Vprince099/ZANDVE/Type-Z/STLs/Panels/Front/README.md

# Credits 
* Parts retrofitted from Voron Trident [VoronDesign](https://github.com/VoronDesign/)
* Adapted to include accent pieces since front frame is 2040
