Vprince099/ZANDVE/User_Mods/LTSPENNY/ZANDVE/L_Stepper_Pillow_Bearing/Images/IMG3.JPG

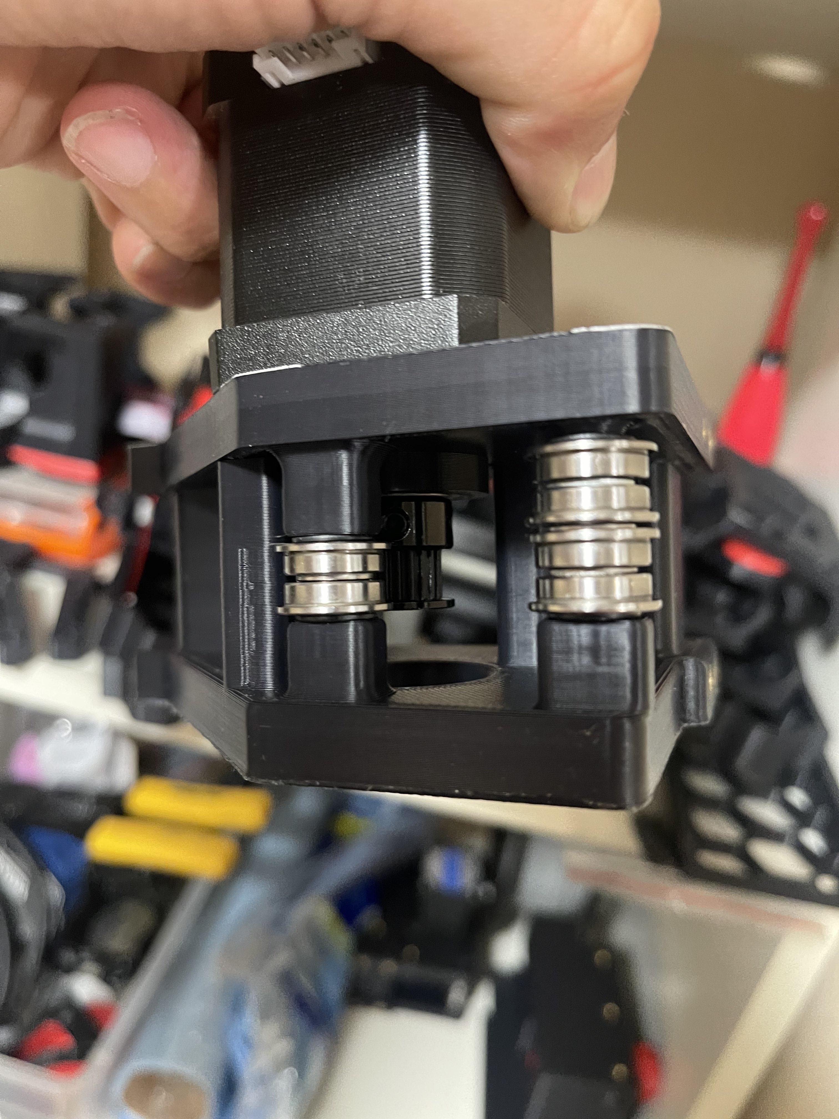
User_Mods/LTSPENNY/ZANDVE/L_Stepper_Pillow_Bearing/Images/IMG3.JPG
