Vprince099/ZANDVE/Type-V/STLs/Panels/Rear/Corner Panel Retainer 3mm x2.stl

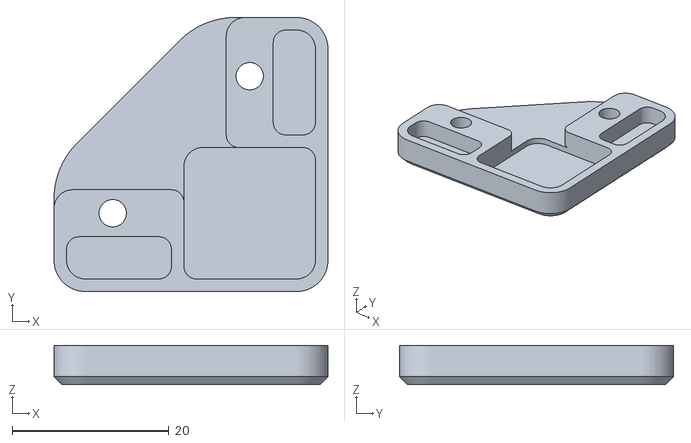
[picture p20: CAD file, 2023-03-26]
Type-V/STLs/Panels/Rear/Corner Panel Retainer 3mm x2.stl
35.0 x 35.0 x 5.00
