Vprince099/ZANDVE/Type-V/STLs/Skirt/PostBuild_Parts/Bottom Panel/bottom_panel_hinge_x2.stl

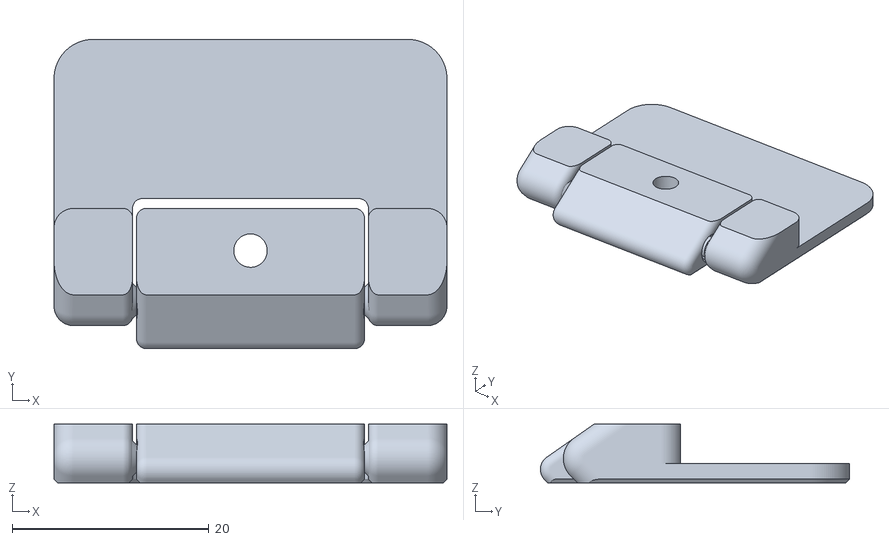
[picture p21: CAD file, 2023-04-10]
Type-V/STLs/Skirt/PostBuild_Parts/Bottom Panel/bottom_panel_hinge_x2.stl
40.0 x 31.5 x 6.00
