Vprince099/ZANDVE/Type-V/STLs/Skirt/PostBuild_Parts/Front/[a]_skirt_logo_x2.stl

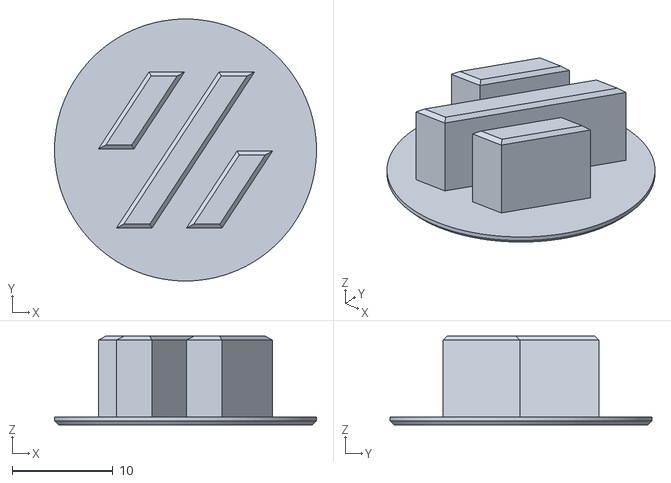
[picture p22: CAD file, 2023-04-05]
Type-V/STLs/Skirt/PostBuild_Parts/Front/[a]_skirt_logo_x2.stl
26.0 x 26.0 x 8.80
