Vprince099/ZANDVE/Type-V/STLs/Skirt/PostBuild_Parts/Rear/Rear_Center_Skirt_E5Plus_Type_V.stl

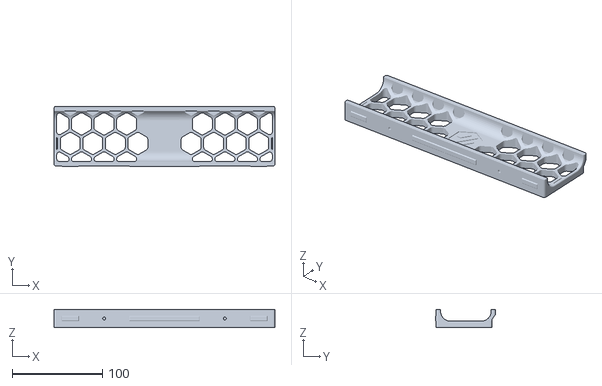
[picture p23: CAD file, 2023-04-05]
Type-V/STLs/Skirt/PostBuild_Parts/Rear/Rear_Center_Skirt_E5Plus_Type_V.stl
245.0 x 66.8 x 20.0
