Vprince099/ZANDVE/Type-V/STLs/Skirt/PostBuild_Parts/Sides/[a]_fan_grill_b_x2.stl

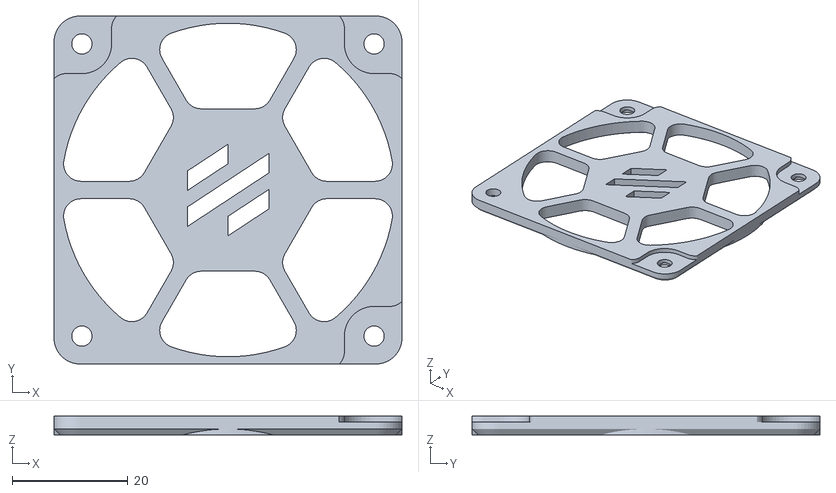
[picture p24: CAD file, 2023-04-05]
Type-V/STLs/Skirt/PostBuild_Parts/Sides/[a]_fan_grill_b_x2.stl
60.0 x 60.0 x 3.20
