Vprince099/ZANDVE/Type-V/STLs/Skirt/PreBuild_Parts/Corners/[a]_corner_baseplate_b_x2.stl

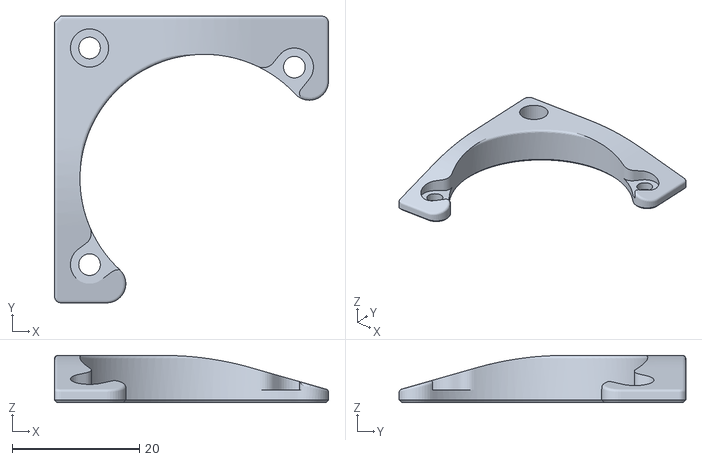
[picture p25: CAD file, 2023-03-27]
Type-V/STLs/Skirt/PreBuild_Parts/Corners/[a]_corner_baseplate_b_x2.stl
43.0 x 45.0 x 7.40
