Vprince099/ZANDVE/Type-V/STLs/Skirt/PreBuild_Parts/Screen/[a]_mini12864_case_front_insert.stl

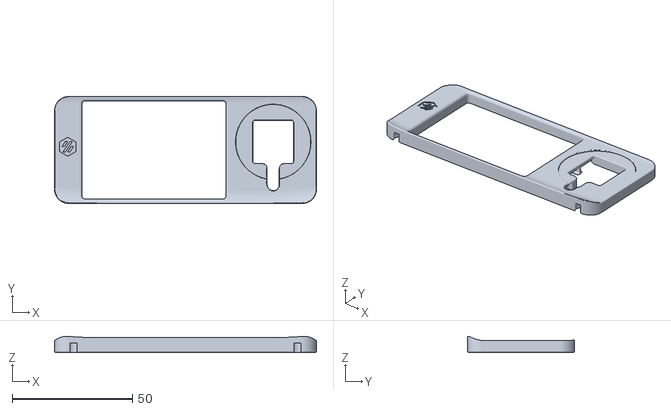
[picture p27: CAD file, 2023-04-05]
Type-V/STLs/Skirt/PreBuild_Parts/Screen/[a]_mini12864_case_front_insert.stl
109.0 x 44.6 x 6.81
