Vprince099/ZANDVE/Type-V/STLs/Tension_Towers/Left/L_Frame_Enclosure_WSupp.stl

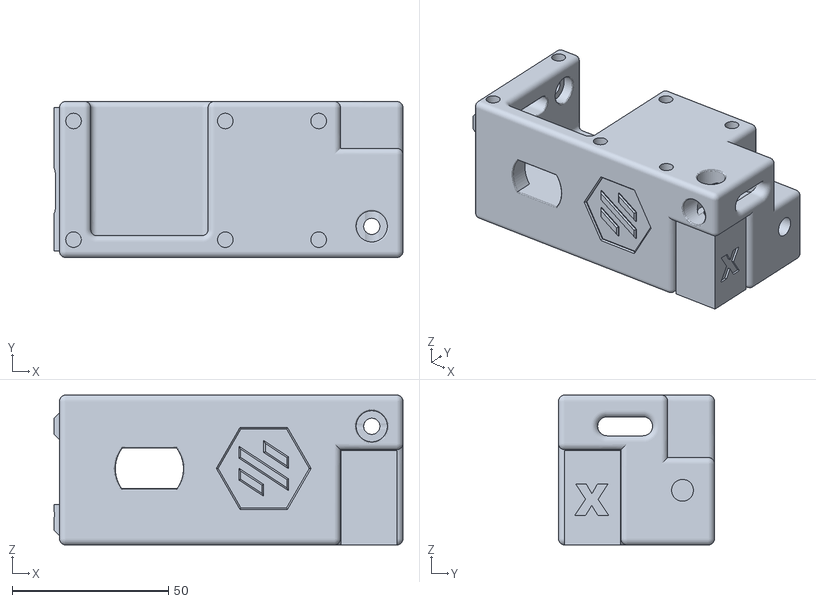
[picture p28: CAD file, 2023-04-05]
Type-V/STLs/Tension_Towers/Left/L_Frame_Enclosure_WSupp.stl
111.8 x 50.0 x 48.0
