Vprince099/ZANDVE/Type-V/STLs/Tools/ZeroGCube30x30.stl

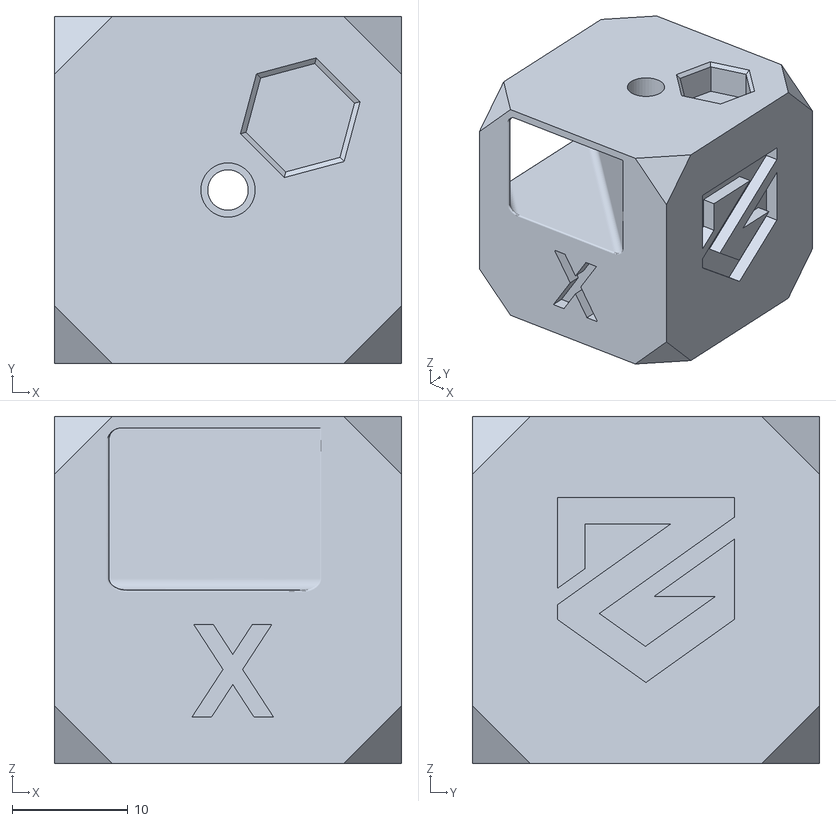
[picture p29: CAD file, 2023-03-27]
Type-V/STLs/Tools/ZeroGCube30x30.stl
30.0 x 30.0 x 30.0
