Vprince099/ZANDVE/Type-V/STLs/Top_Hat_STD/TH_Front_Left/FL Front Panel Lid[acc].stl

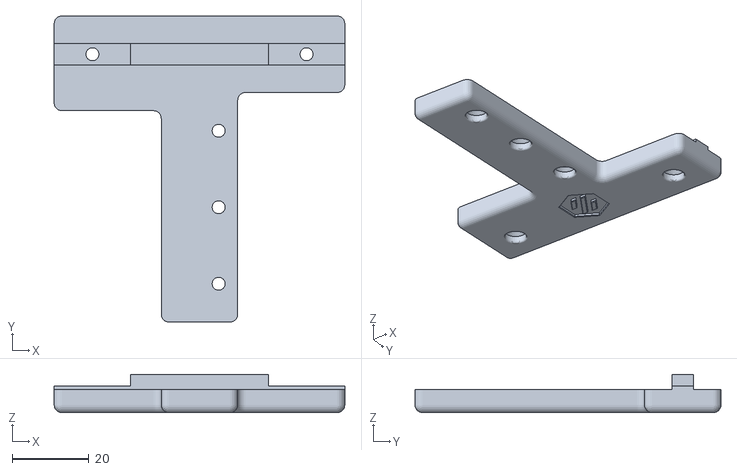
[picture p30: CAD file, 2023-04-05]
Type-V/STLs/Top_Hat_STD/TH_Front_Left/FL Front Panel Lid[acc].stl
76.0 x 80.0 x 10.0
