Vprince099/ZANDVE/Type-V/STLs/Top_Hat_STD/TH_Rear/Rear Panel - Right.stl

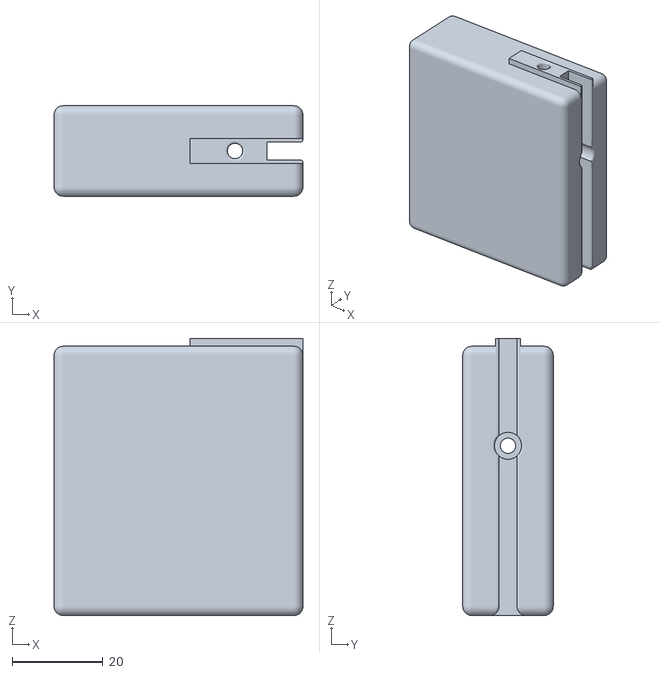
[picture p31: CAD file, 2023-03-26]
Type-V/STLs/Top_Hat_STD/TH_Rear/Rear Panel - Right.stl
55.0 x 20.0 x 61.2
