Vprince099/ZANDVE/Type-V/STLs/Top_Hat_STD/TH_Rear_Left/RL Corner With Support.stl

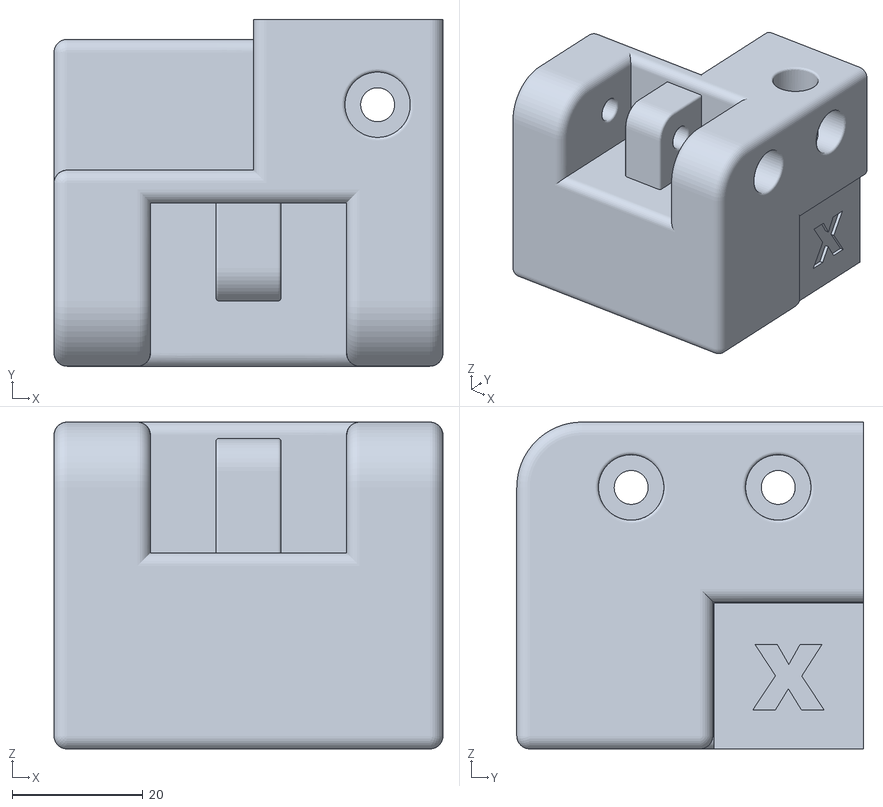
[picture p32: CAD file, 2023-04-02]
Type-V/STLs/Top_Hat_STD/TH_Rear_Left/RL Corner With Support.stl
59.5 x 53.0 x 50.0
