Vprince099/ZANDVE/Type-V/STLs/Top_Hat_XL/TH_Rear/Rear Panel - Center.stl

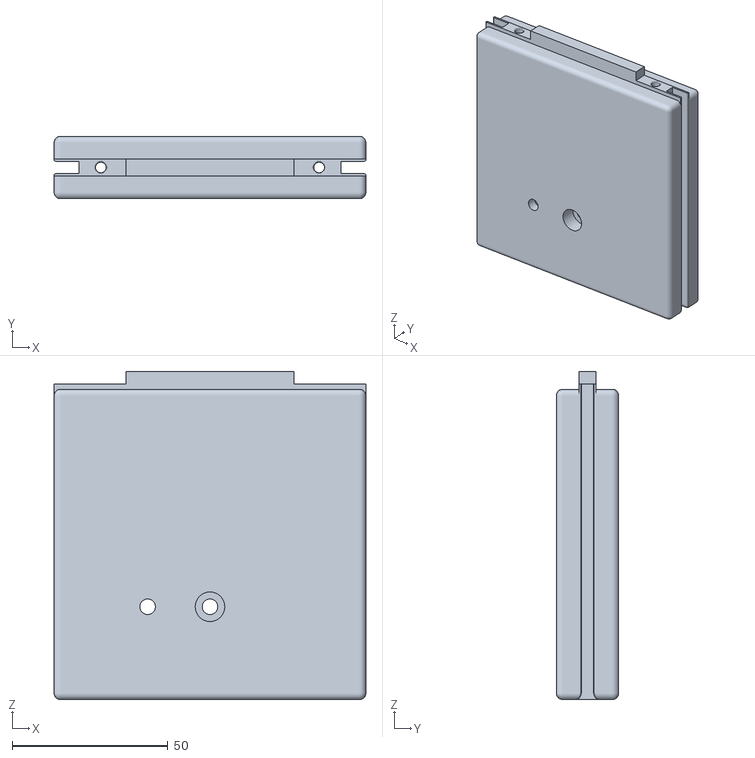
[picture p34: CAD file, 2023-04-01]
Type-V/STLs/Top_Hat_XL/TH_Rear/Rear Panel - Center.stl
100.0 x 20.0 x 105.2
