Vprince099/ZANDVE/Type-V/STLs/X-Gantry/Left/L_Top_Left.stl

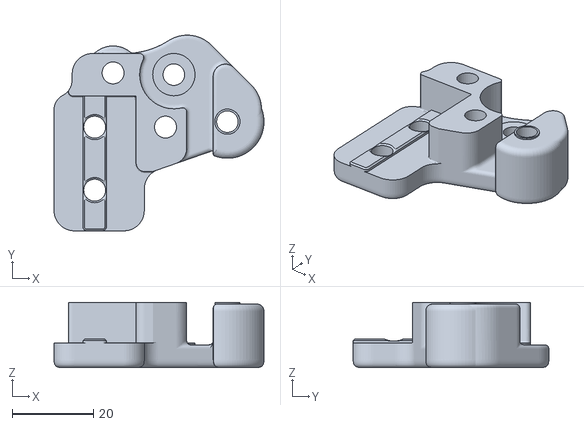
[picture p35: CAD file, 2023-03-27]
Type-V/STLs/X-Gantry/Left/L_Top_Left.stl
51.6 x 48.1 x 16.0
