Vprince099/ZANDVE/Type-V/STLs/X-Gantry/Right/R_Bottom_right.stl

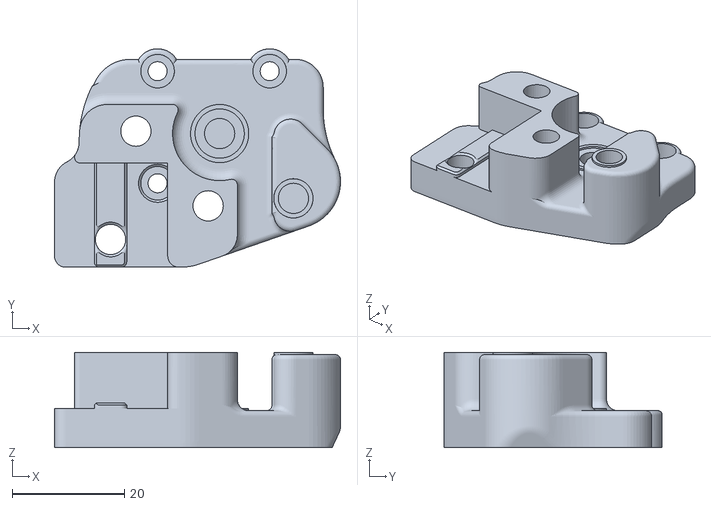
[picture p36: CAD file, 2023-03-27]
Type-V/STLs/X-Gantry/Right/R_Bottom_right.stl
51.0 x 39.0 x 17.0
