Vprince099/ZANDVE/Type-V/STLs/Z_Motion/wago_221-412_mount.stl

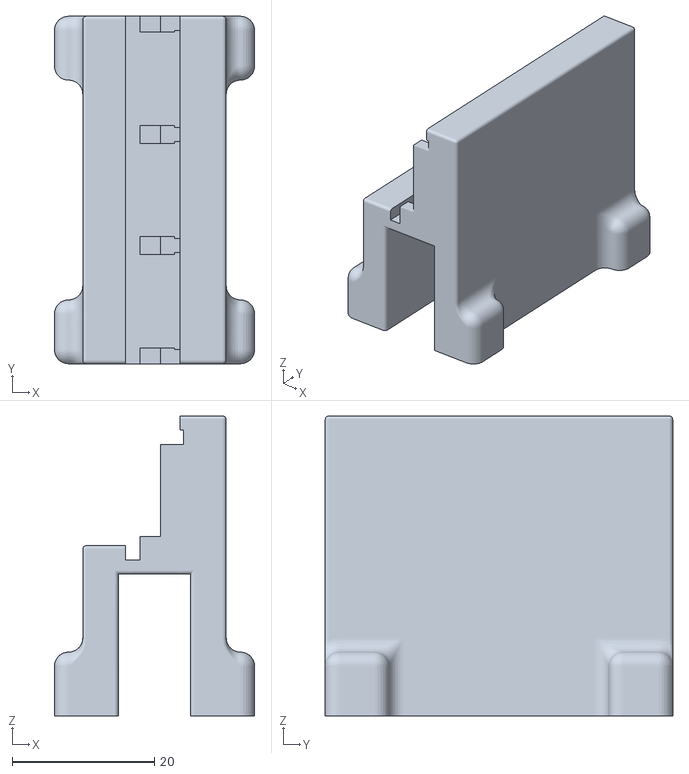
[picture p37: CAD file, 2023-03-27]
Type-V/STLs/Z_Motion/wago_221-412_mount.stl
28.2 x 49.0 x 42.2
