Vprince099/ZANDVE/Type-Z/STLs/Limit_Switch_Mounts/Klicky Dock Mount.stl

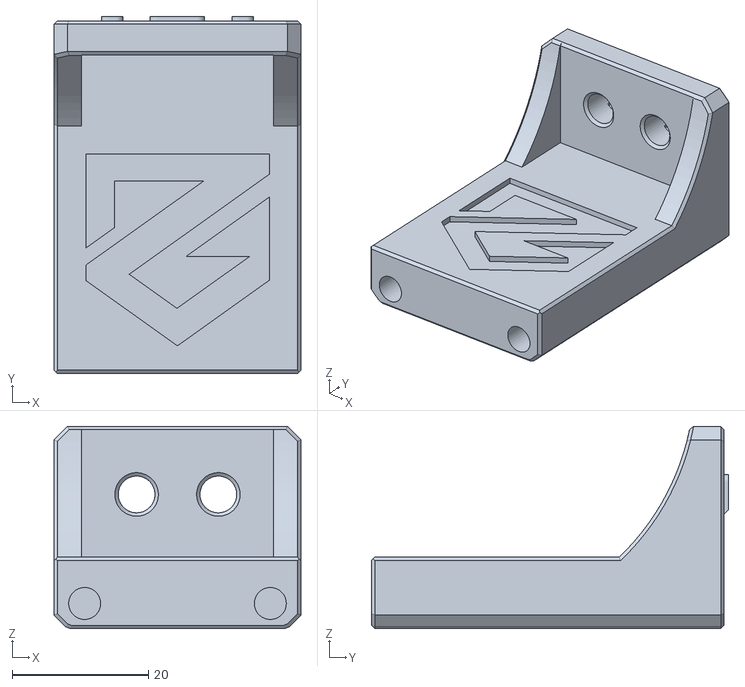
[picture p38: CAD file, 2023-03-27]
Type-Z/STLs/Limit_Switch_Mounts/Klicky Dock Mount.stl
36.3 x 52.4 x 29.7
