Vprince099/ZANDVE/Type-Z/STLs/Panels/Gantry/Rear/Rear Panel Base - Left.stl

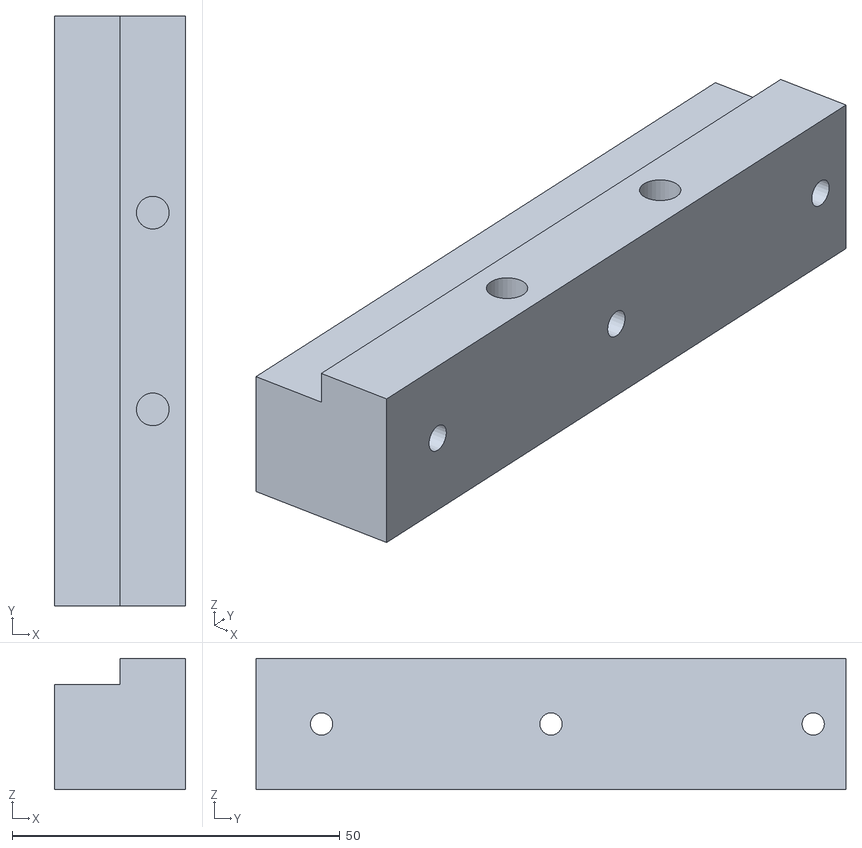
[picture p39: CAD file, 2023-05-07]
Type-Z/STLs/Panels/Gantry/Rear/Rear Panel Base - Left.stl
20.0 x 90.0 x 20.0
