Vprince099/ZANDVE/Type-Z/STLs/Panels/Rear/Type-Z_2020_Endcap_Cover.stl

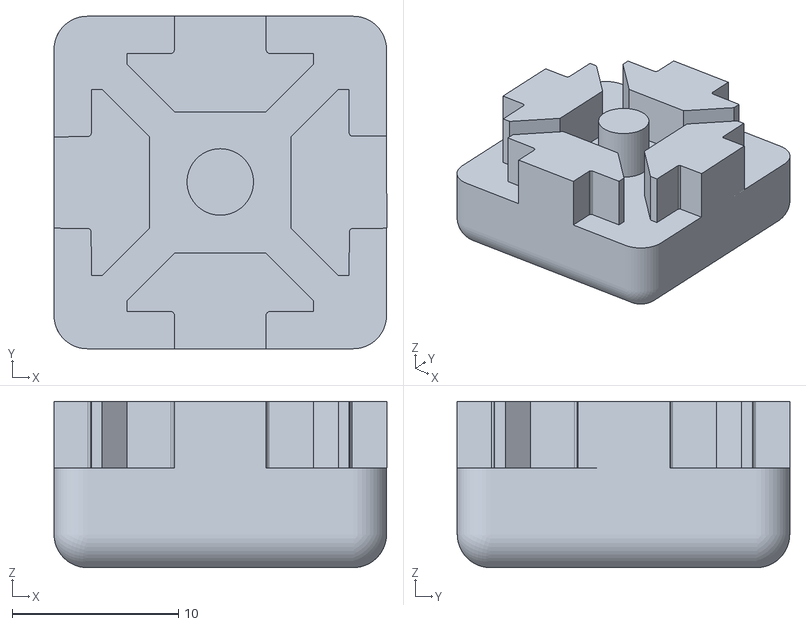
[picture p40: CAD file, 2023-03-27]
Type-Z/STLs/Panels/Rear/Type-Z_2020_Endcap_Cover.stl
20.0 x 20.0 x 10.0
