Vprince099/ZANDVE/Type-Z/STLs/Rear_Steppers/Max Power/Left/L Bottom Plate MP.stl

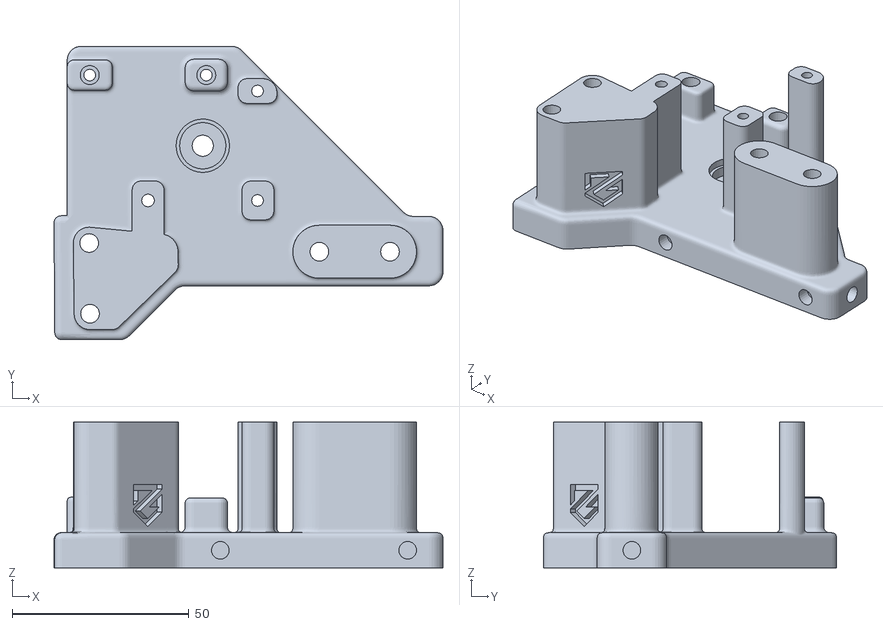
[picture p41: CAD file, 2023-05-07]
Type-Z/STLs/Rear_Steppers/Max Power/Left/L Bottom Plate MP.stl
110.1 x 83.1 x 41.3
