Vprince099/ZANDVE/Type-Z/STLs/Skirt/PostBuild_Parts/Front/ZeroG Insert Right[acc].stl

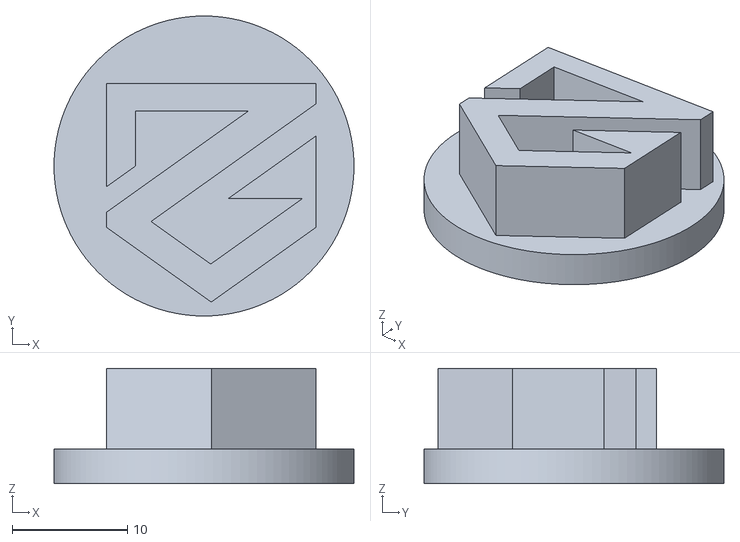
[picture p43: CAD file, 2023-03-27]
Type-Z/STLs/Skirt/PostBuild_Parts/Front/ZeroG Insert Right[acc].stl
26.0 x 26.0 x 10.0
