Vprince099/ZANDVE/Type-Z/STLs/Skirt/PostBuild_Parts/Sides/[a]type_z_fan_grill_a_x2.stl

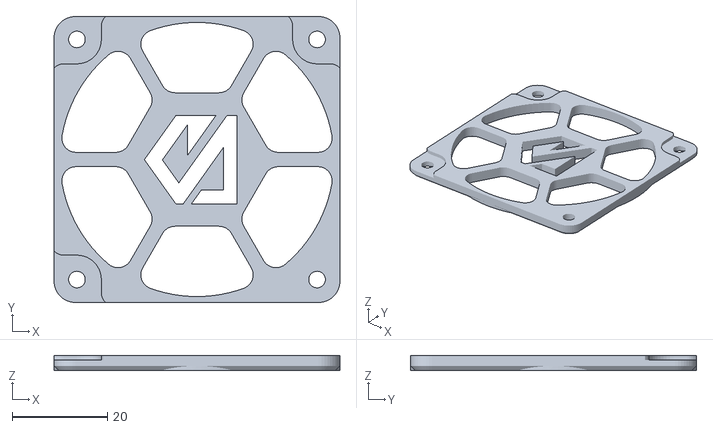
[picture p44: CAD file, 2023-03-27]
Type-Z/STLs/Skirt/PostBuild_Parts/Sides/[a]type_z_fan_grill_a_x2.stl
60.0 x 60.0 x 3.20
