Vprince099/ZANDVE/Type-Z/STLs/Top_Hat/TH_Rear_Left/RR Panel Base.stl

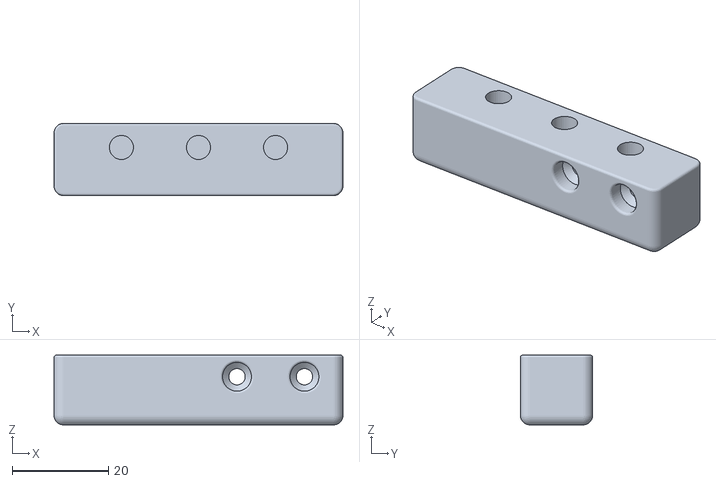
[picture p45: CAD file, 2023-03-26]
Type-Z/STLs/Top_Hat/TH_Rear_Left/RR Panel Base.stl
60.0 x 15.0 x 14.5
