Vprince099/ZANDVE/User_Mods/JellyBob/ZANDVE_Less-Frame/STL's/L_Less_Frame_Enclosure_WSupp.stl

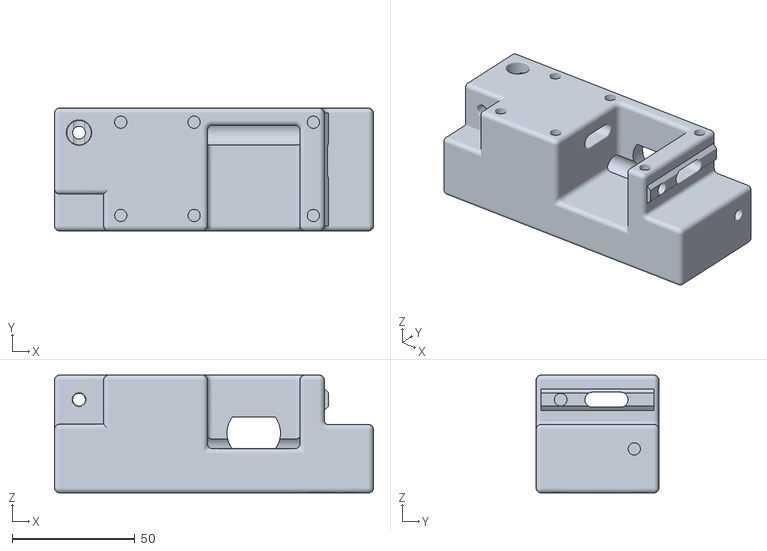
[picture p46: CAD file, 2023-04-02]
User_Mods/JellyBob/ZANDVE_Less-Frame/STL's/L_Less_Frame_Enclosure_WSupp.stl
130.0 x 50.0 x 48.0
