Vprince099/ZANDVE/User_Mods/LTSPENNY/ZANDVE/L_Stepper_Pillow_Bearing/STLs/Left_Stepper_Pillow_Block_Mod.stl

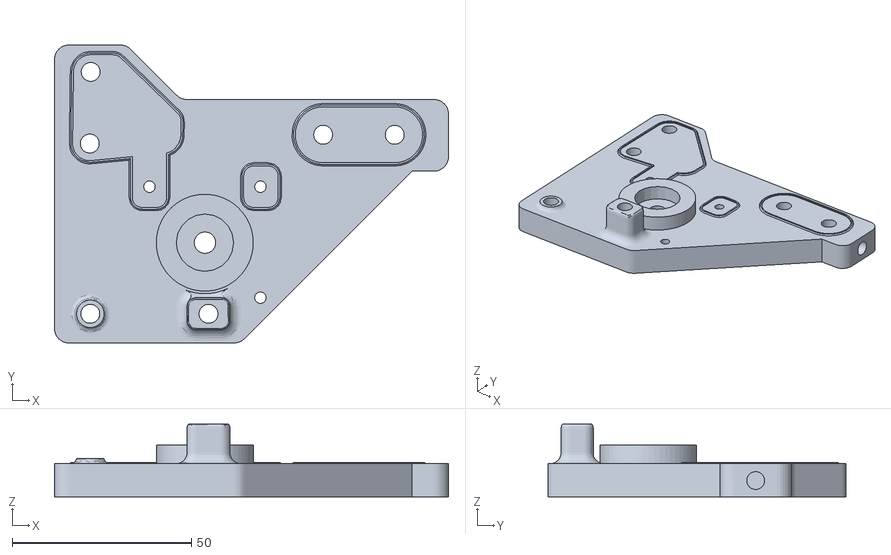
[picture p47: CAD file, 2023-04-13]
User_Mods/LTSPENNY/ZANDVE/L_Stepper_Pillow_Bearing/STLs/Left_Stepper_Pillow_Block_Mod.stl
110.0 x 83.2 x 20.3
