Vprince099/ZANDVE/Type-V/STLs/Electronics/DIN_frame_mount_x4_corrected.stl

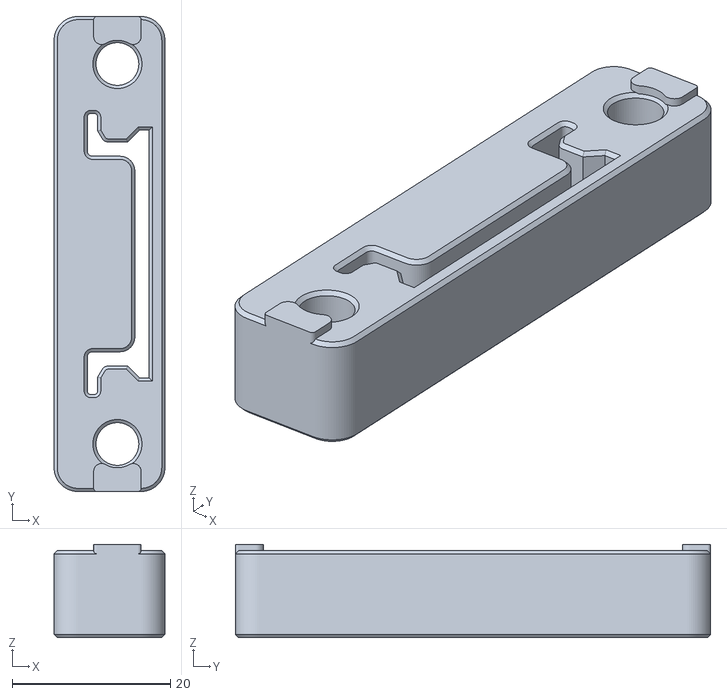
[picture p48: CAD file, 2023-03-27]
Type-V/STLs/Electronics/DIN_frame_mount_x4_corrected.stl
14.0 x 60.0 x 11.8
