Vprince099/ZANDVE/Type-V/STLs/Limit_Switch_Mounts/X Endstop.stl

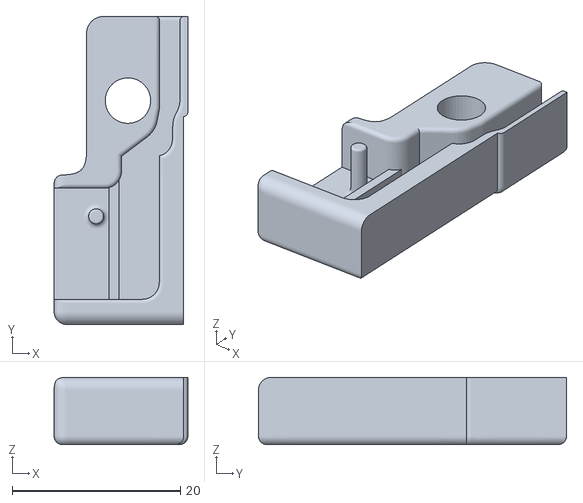
[picture p49: CAD file, 2023-03-27]
Type-V/STLs/Limit_Switch_Mounts/X Endstop.stl
15.9 x 36.6 x 8.00
