Vprince099/ZANDVE/Type-V/STLs/Panels/Front/Hinge_Cover_Top_Left[acc].stl

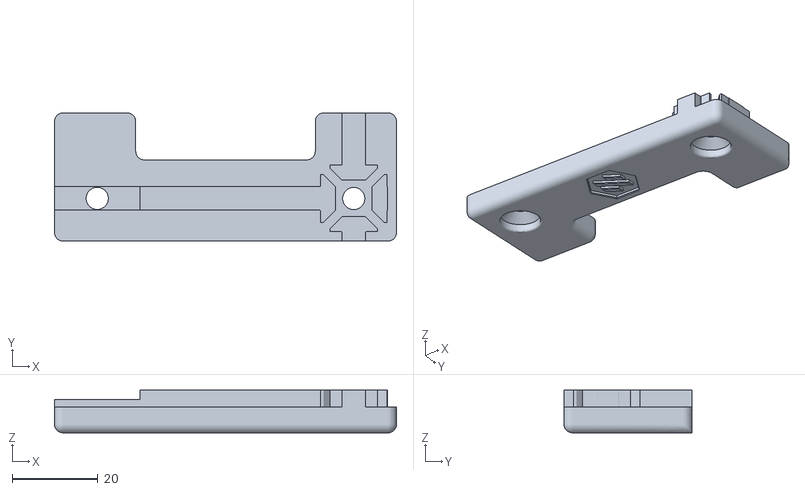
[picture p50: CAD file, 2023-04-05]
Type-V/STLs/Panels/Front/Hinge_Cover_Top_Left[acc].stl
80.0 x 30.0 x 10.0
