Vprince099/ZANDVE/Type-V/STLs/Panels/Gantry/Left/Rear Panel Lid.stl

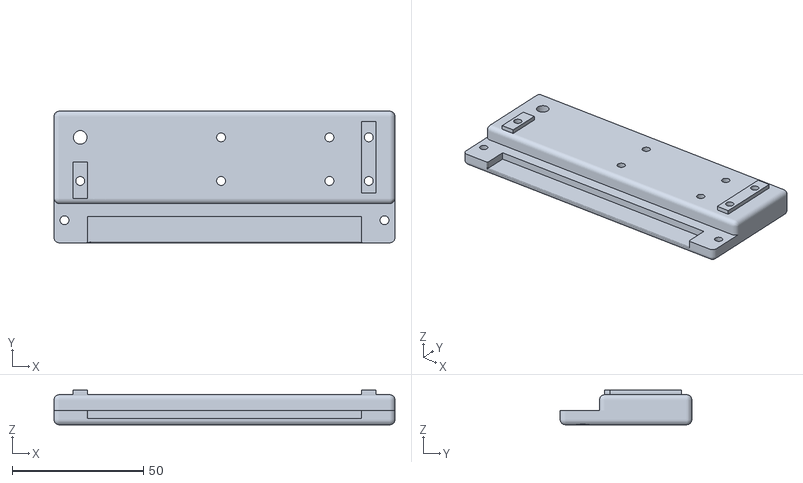
[picture p51: CAD file, 2023-03-26]
Type-V/STLs/Panels/Gantry/Left/Rear Panel Lid.stl
130.0 x 50.2 x 13.2
