Vprince099/ZANDVE/Type-V/STLs/Panels/Gantry/Right/X Panel Lid x8.stl

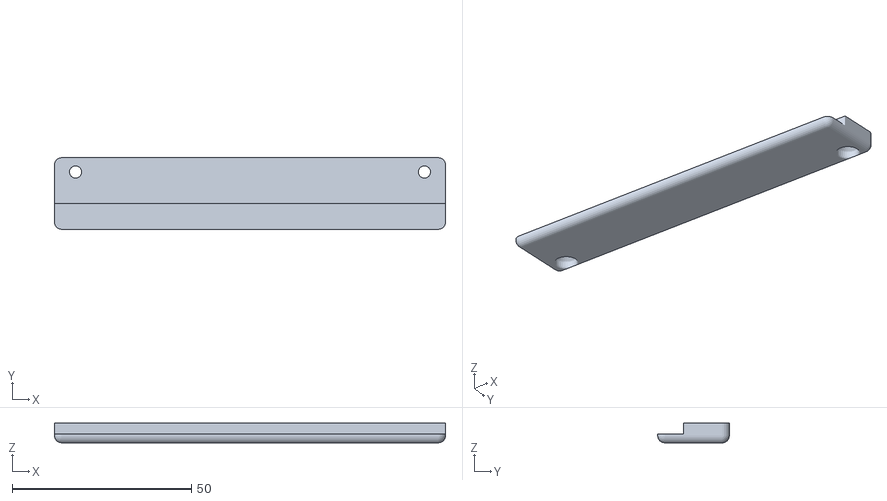
[picture p52: CAD file, 2023-03-26]
Type-V/STLs/Panels/Gantry/Right/X Panel Lid x8.stl
109.0 x 20.0 x 5.50
