Vprince099/ZANDVE/Type-V/STLs/Skirt/PostBuild_Parts/Bottom Panel/bottom_panel_clip_x4.stl

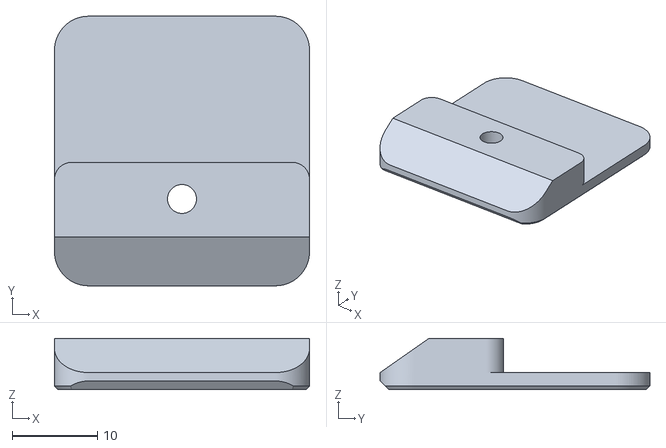
[picture p53: CAD file, 2023-04-10]
Type-V/STLs/Skirt/PostBuild_Parts/Bottom Panel/bottom_panel_clip_x4.stl
30.0 x 31.7 x 6.00
