Vprince099/ZANDVE/Type-V/STLs/Skirt/PostBuild_Parts/Front/Skirt_E5+_Front_Left.stl

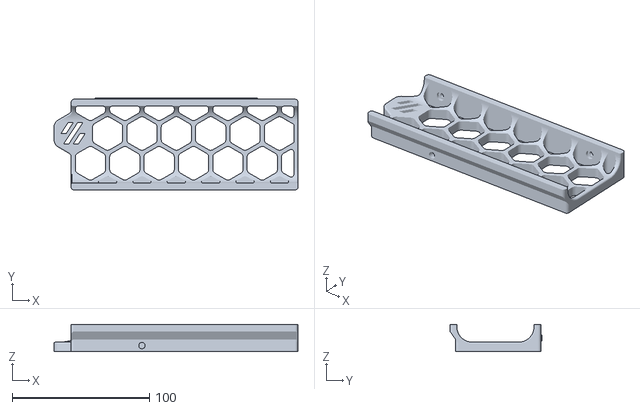
[picture p54: CAD file, 2023-04-05]
Type-V/STLs/Skirt/PostBuild_Parts/Front/Skirt_E5+_Front_Left.stl
177.5 x 66.8 x 20.0
