Vprince099/ZANDVE/Type-V/STLs/Skirt/PreBuild_Parts/Rear_IO/keystone_panel.stl

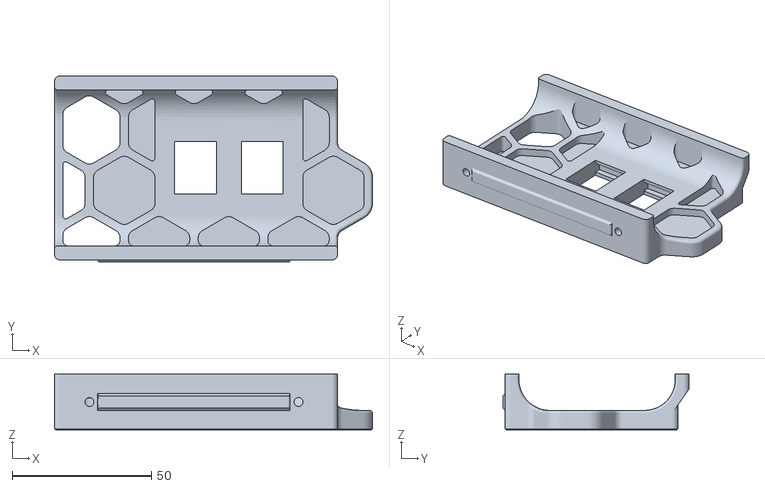
[picture p55: CAD file, 2023-03-27]
Type-V/STLs/Skirt/PreBuild_Parts/Rear_IO/keystone_panel.stl
114.0 x 66.8 x 20.0
