Vprince099/ZANDVE/Type-V/STLs/Skirt/PreBuild_Parts/Screen/mini12864_case_rear.stl

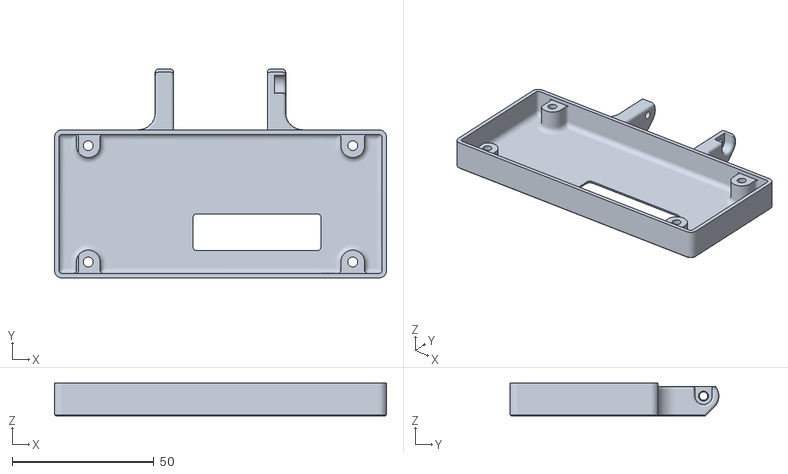
[picture p56: CAD file, 2023-03-27]
Type-V/STLs/Skirt/PreBuild_Parts/Screen/mini12864_case_rear.stl
117.0 x 73.6 x 11.6
