Vprince099/ZANDVE/Type-V/STLs/Tension_Towers/Left/L_Tensioner[acc].stl

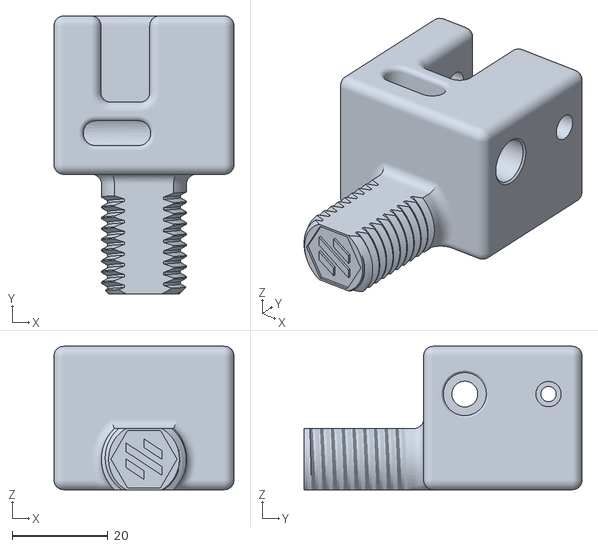
[picture p57: CAD file, 2023-04-05]
Type-V/STLs/Tension_Towers/Left/L_Tensioner[acc].stl
37.6 x 58.1 x 30.0
