Vprince099/ZANDVE/Type-V/STLs/Tools/Rail alignment tool x 2.stl

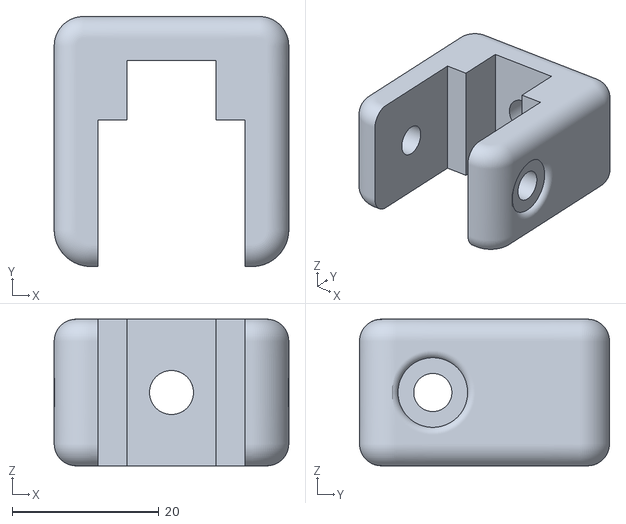
[picture p58: CAD file, 2023-03-27]
Type-V/STLs/Tools/Rail alignment tool x 2.stl
32.0 x 34.1 x 20.0
