Vprince099/ZANDVE/Type-V/STLs/Top_Hat_STD/TH_Front_Left/FL Inner Panel Lid.stl

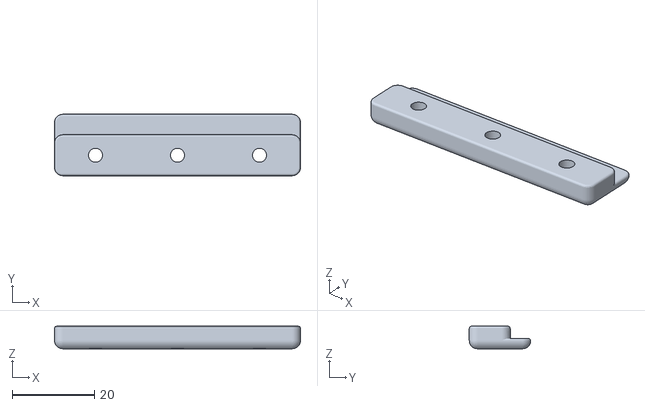
[picture p59: CAD file, 2023-03-26]
Type-V/STLs/Top_Hat_STD/TH_Front_Left/FL Inner Panel Lid.stl
60.0 x 15.0 x 5.50
