Vprince099/ZANDVE/Type-V/STLs/Top_Hat_STD/TH_Front_Right/FR Top Clip[acc].stl

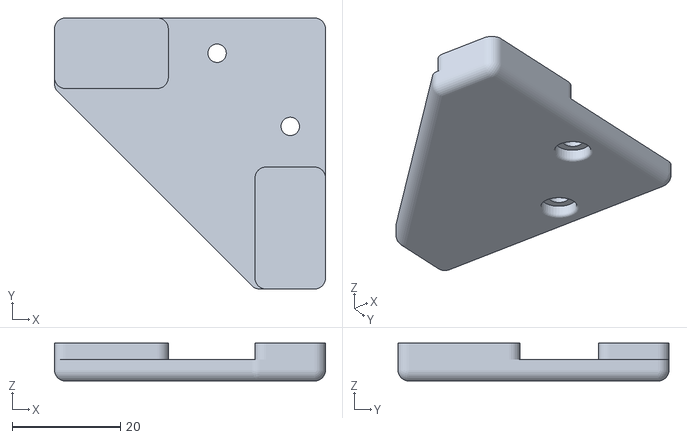
[picture p60: CAD file, 2023-03-26]
Type-V/STLs/Top_Hat_STD/TH_Front_Right/FR Top Clip[acc].stl
50.0 x 50.0 x 7.00
