Vprince099/ZANDVE/Type-V/STLs/Top_Hat_STD/TH_Rear_Right/RR Hinge[acc].stl

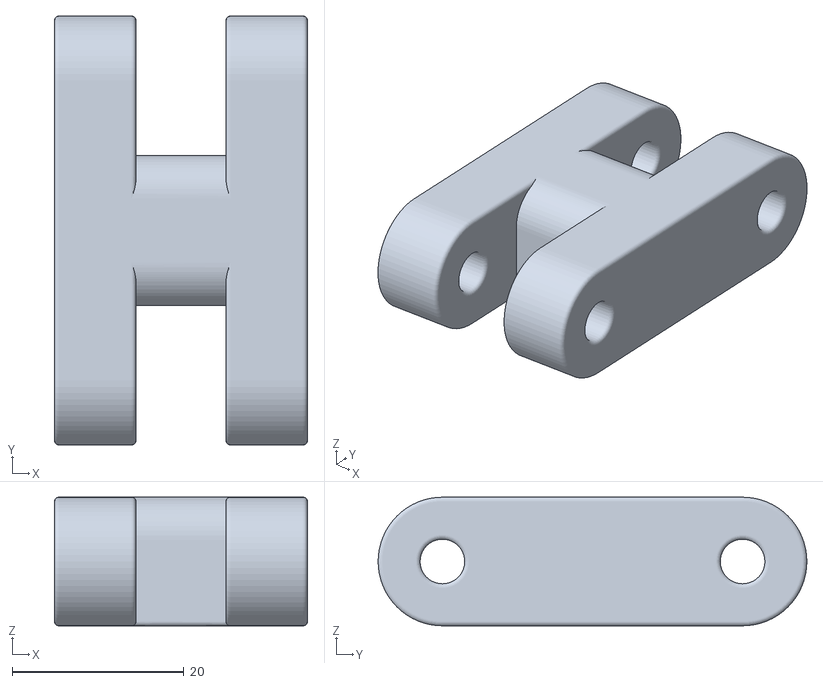
[picture p61: CAD file, 2023-03-26]
Type-V/STLs/Top_Hat_STD/TH_Rear_Right/RR Hinge[acc].stl
29.5 x 50.0 x 15.0
