Vprince099/ZANDVE/Type-V/STLs/Top_Hat_XL/TH_Front_Left/FL Inner Panel Lid.stl

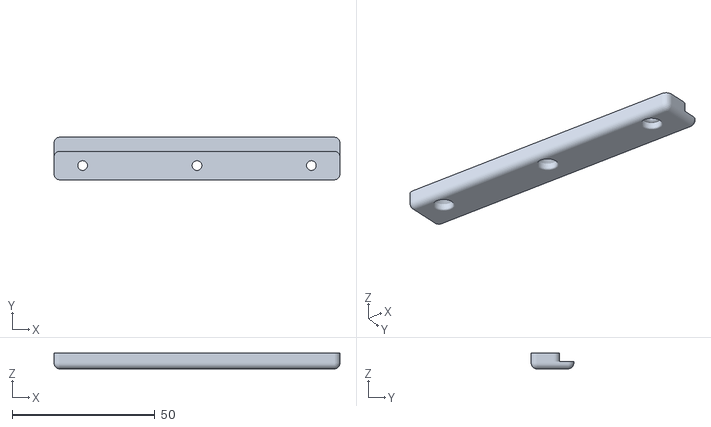
[picture p62: CAD file, 2023-04-01]
Type-V/STLs/Top_Hat_XL/TH_Front_Left/FL Inner Panel Lid.stl
100.0 x 14.9 x 5.50
