Vprince099/ZANDVE/Type-V/STLs/Top_Hat_XL/TH_Front_Right/FR Lock Body.stl

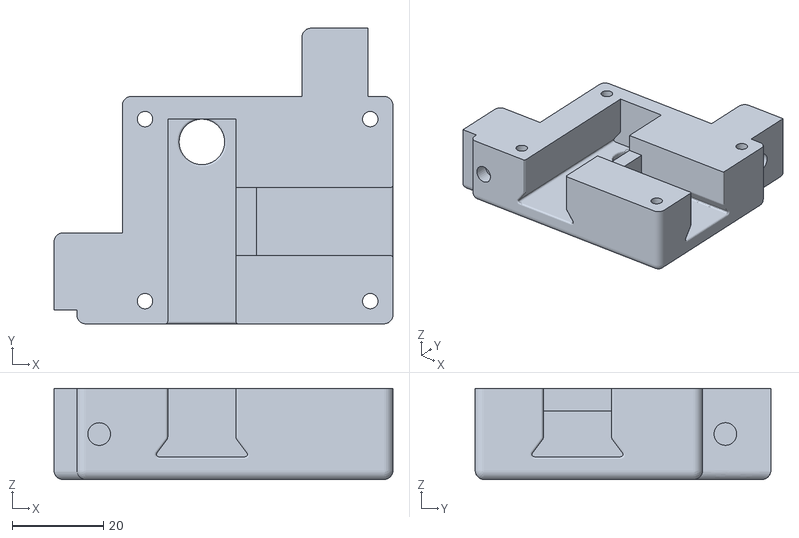
[picture p63: CAD file, 2023-04-01]
Type-V/STLs/Top_Hat_XL/TH_Front_Right/FR Lock Body.stl
74.5 x 65.0 x 20.0
