Vprince099/ZANDVE/Type-V/STLs/Top_Hat_XL/TH_Rear/Rear Panel - Right.stl

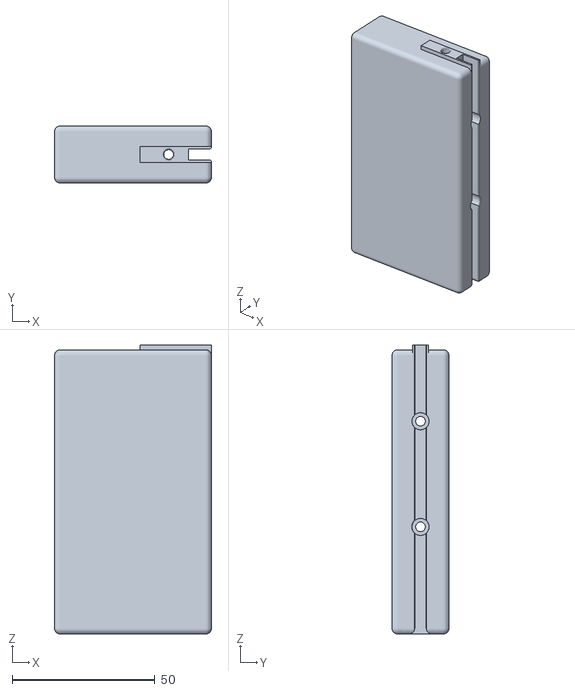
[picture p64: CAD file, 2023-04-01]
Type-V/STLs/Top_Hat_XL/TH_Rear/Rear Panel - Right.stl
55.0 x 20.0 x 101.2
