Vprince099/ZANDVE/Type-V/STLs/Top_Hat_XL/TH_Rear_Right/RR Base.stl

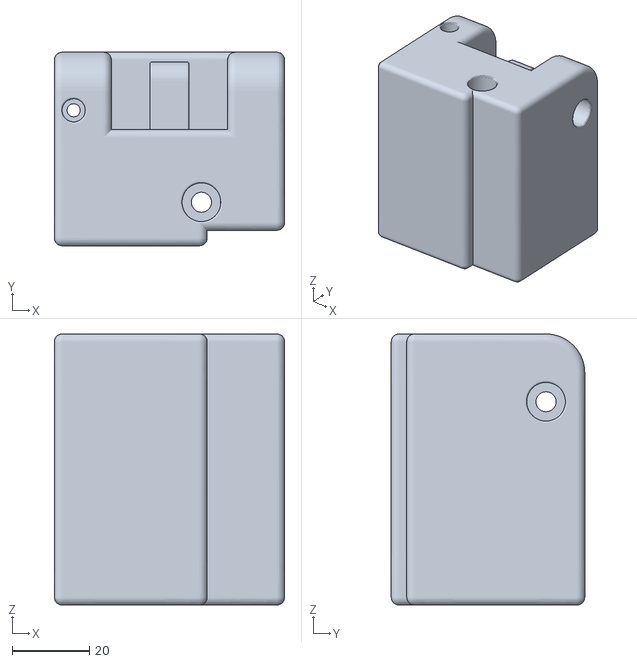
[picture p65: CAD file, 2023-04-01]
Type-V/STLs/Top_Hat_XL/TH_Rear_Right/RR Base.stl
59.5 x 50.0 x 70.0
