Vprince099/ZANDVE/Type-V/STLs/X-Gantry/Left/L_Bottom_Left.stl

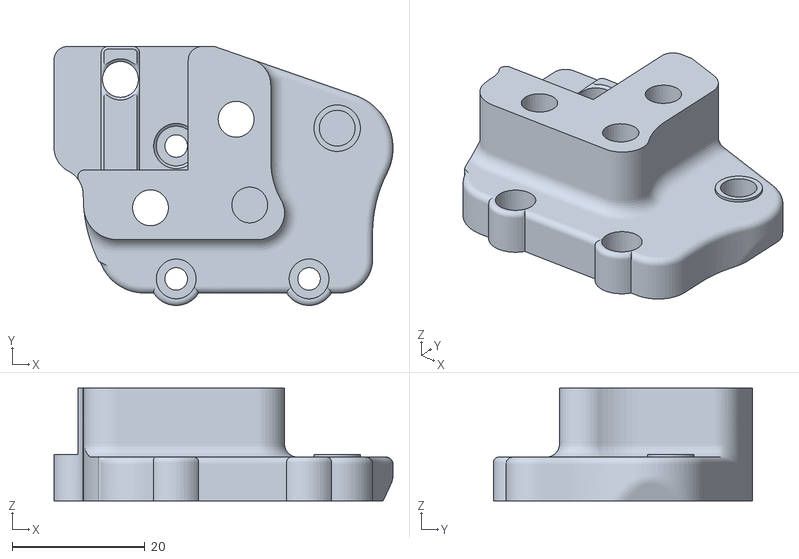
[picture p66: CAD file, 2023-03-27]
Type-V/STLs/X-Gantry/Left/L_Bottom_Left.stl
51.0 x 39.0 x 17.0
