Vprince099/ZANDVE/Type-V/STLs/X-Gantry/Right/R_Top_right.stl

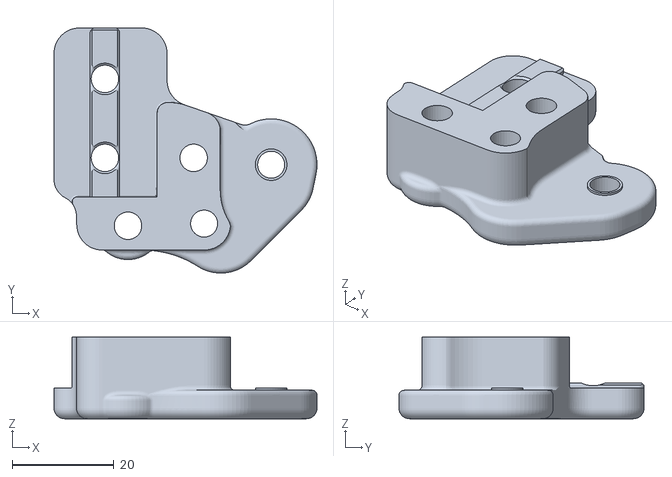
[picture p67: CAD file, 2023-03-27]
Type-V/STLs/X-Gantry/Right/R_Top_right.stl
51.6 x 48.1 x 16.0
