Vprince099/ZANDVE/Type-V/STLs/Z_Motion/Wago Mount Lid.stl

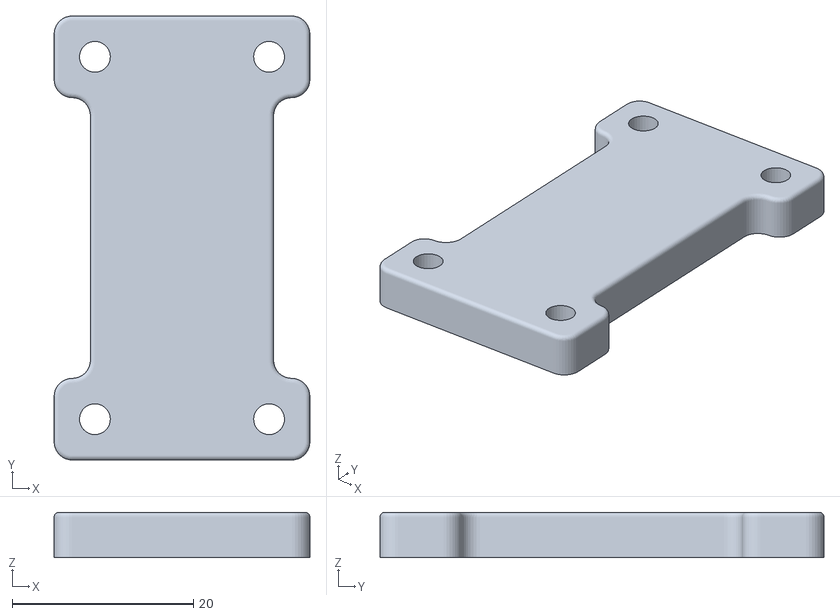
[picture p68: CAD file, 2023-03-27]
Type-V/STLs/Z_Motion/Wago Mount Lid.stl
28.2 x 49.0 x 5.00
