Vprince099/ZANDVE/Type-Z/STLs/Rear_Steppers/Max Power/Left/L Frame Top Plate.stl

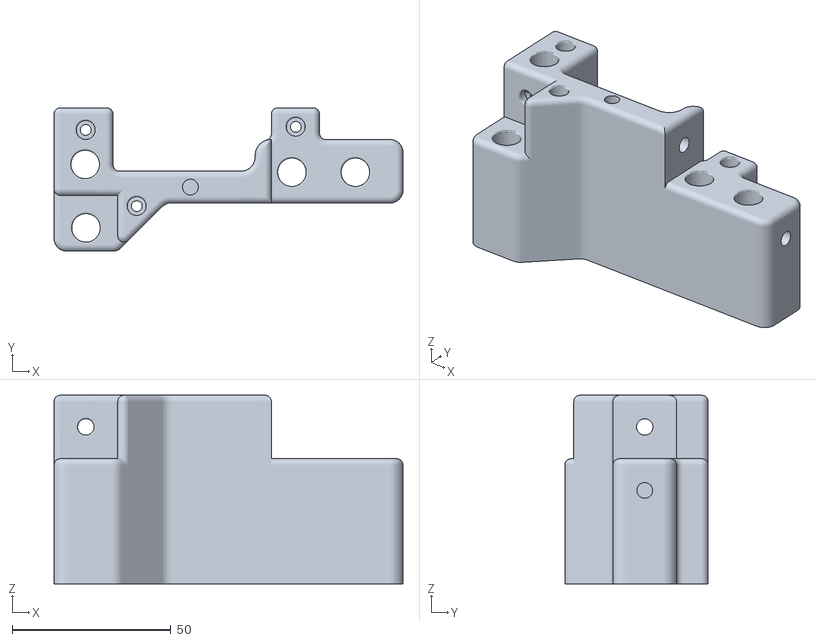
[picture p69: CAD file, 2023-03-26]
Type-Z/STLs/Rear_Steppers/Max Power/Left/L Frame Top Plate.stl
110.0 x 45.2 x 59.5
