Vprince099/ZANDVE/Type-V/STLs/Backpack_Enclosure/[a]_latch_left.stl

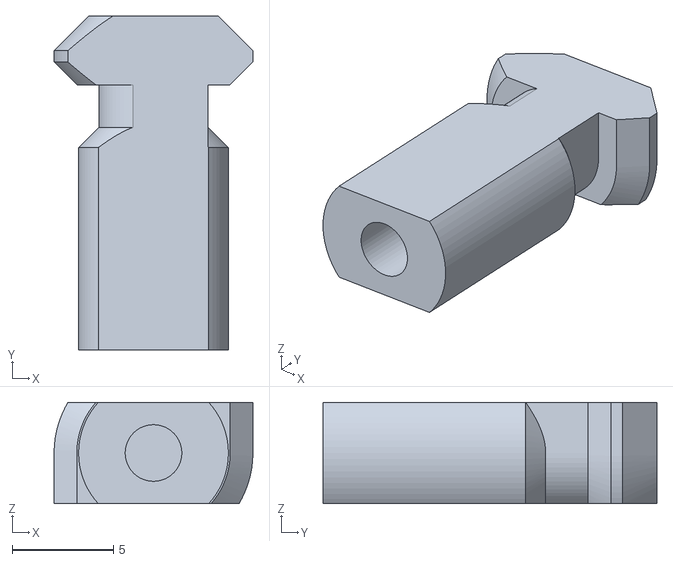
[picture p70: CAD file, 2023-03-27]
Type-V/STLs/Backpack_Enclosure/[a]_latch_left.stl
9.82 x 16.5 x 5.00
