Vprince099/ZANDVE/Type-V/STLs/Electronics/rs25_psu_bracket_clip.stl

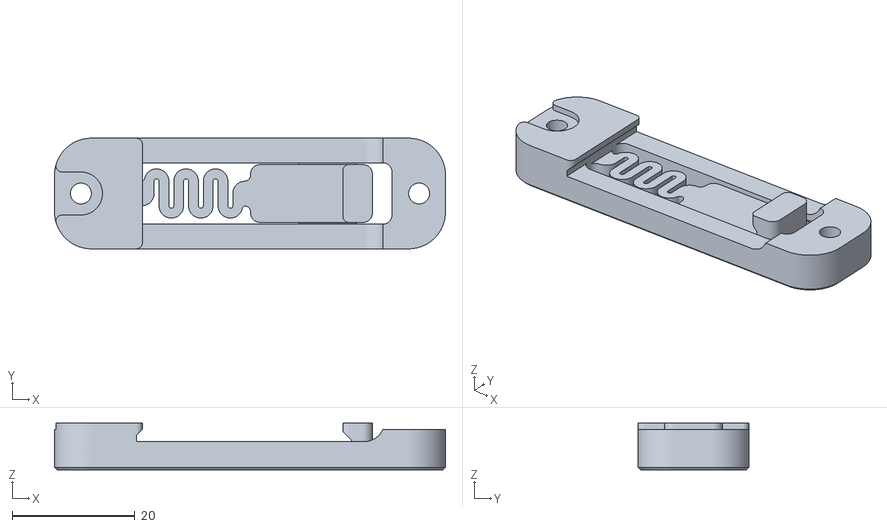
[picture p71: CAD file, 2023-03-27]
Type-V/STLs/Electronics/rs25_psu_bracket_clip.stl
63.6 x 18.0 x 7.60
