Vprince099/ZANDVE/Type-V/STLs/Limit_Switch_Mounts/Beacon_SB_Xcarriage-Right.stl

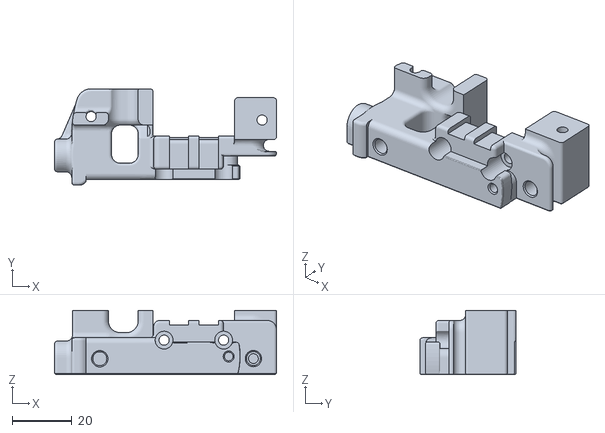
[picture p72: CAD file, 2023-03-27]
Type-V/STLs/Limit_Switch_Mounts/Beacon_SB_Xcarriage-Right.stl
74.6 x 32.4 x 21.6
