Vprince099/ZANDVE/Type-V/STLs/Panels/Deck/Deck Rear Right Panel Clip.stl

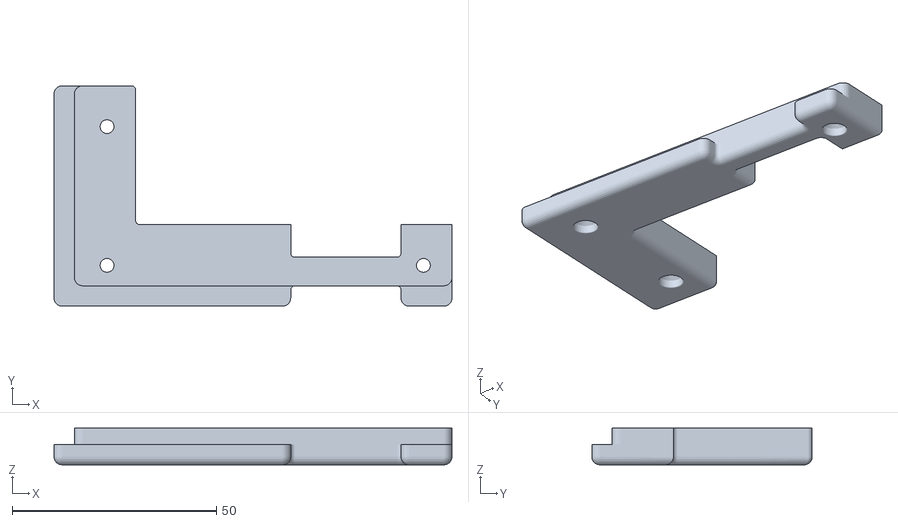
[picture p73: CAD file, 2023-03-26]
Type-V/STLs/Panels/Deck/Deck Rear Right Panel Clip.stl
97.5 x 54.0 x 9.00
