Vprince099/ZANDVE/Type-V/STLs/Panels/Gantry/Left/X Panel Base x8.stl

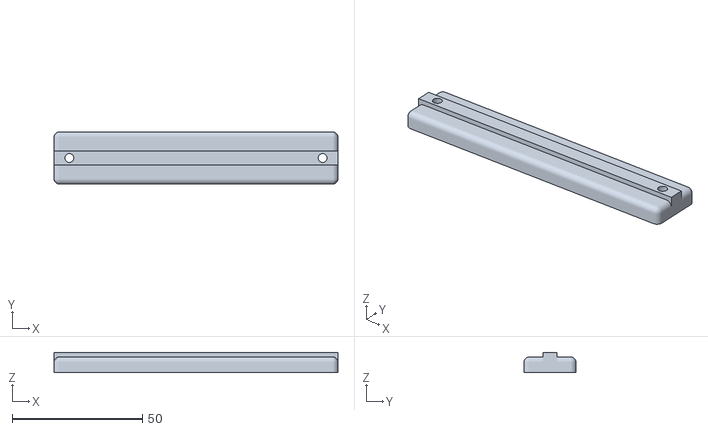
[picture p74: CAD file, 2023-03-26]
Type-V/STLs/Panels/Gantry/Left/X Panel Base x8.stl
109.0 x 20.0 x 7.75
