Vprince099/ZANDVE/Type-V/STLs/Skirt/PostBuild_Parts/Sides/Skirt_E5+_Side_B_x2.stl

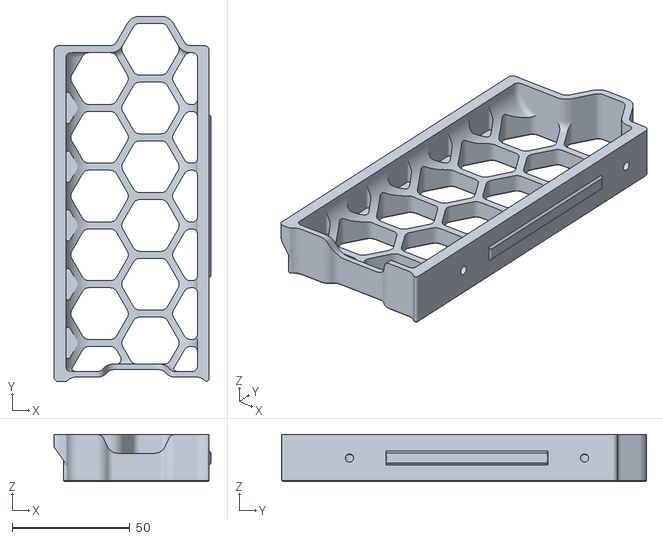
[picture p75: CAD file, 2023-03-27]
Type-V/STLs/Skirt/PostBuild_Parts/Sides/Skirt_E5+_Side_B_x2.stl
66.8 x 155.5 x 20.0
