Vprince099/ZANDVE/Type-V/STLs/Skirt/PreBuild_Parts/Corners/Corner_A_x2.stl

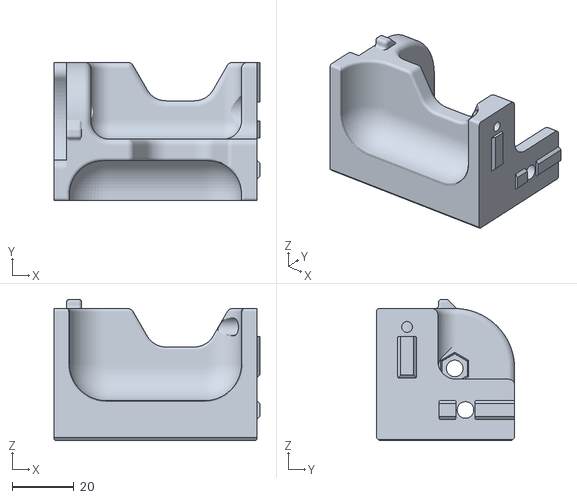
[picture p76: CAD file, 2023-03-27]
Type-V/STLs/Skirt/PreBuild_Parts/Corners/Corner_A_x2.stl
67.0 x 45.0 x 46.0
