Vprince099/ZANDVE/Type-V/STLs/Skirt/PreBuild_Parts/Rear_IO/[a]_keystone_blank_insert_x2.stl

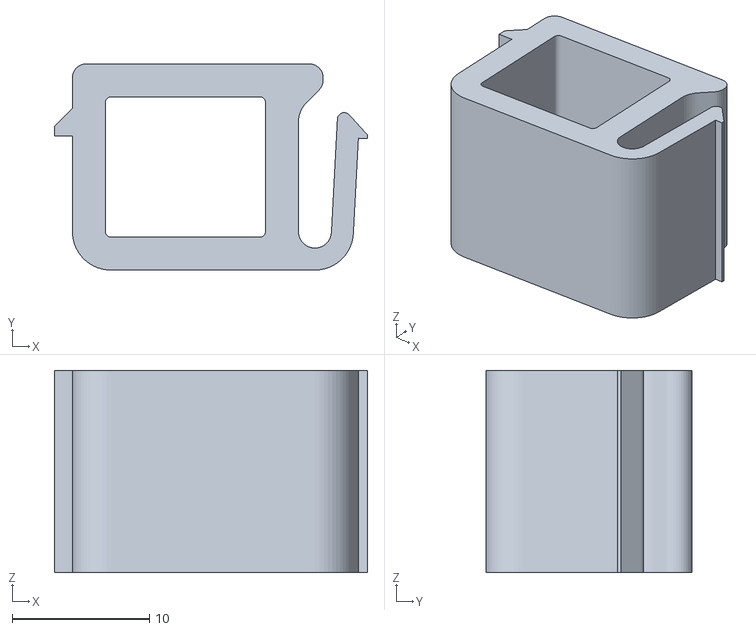
[picture p77: CAD file, 2023-03-27]
Type-V/STLs/Skirt/PreBuild_Parts/Rear_IO/[a]_keystone_blank_insert_x2.stl
22.8 x 15.0 x 14.7
