Vprince099/ZANDVE/Type-V/STLs/Skirt/PreBuild_Parts/Screen/mini12864_case_front.stl

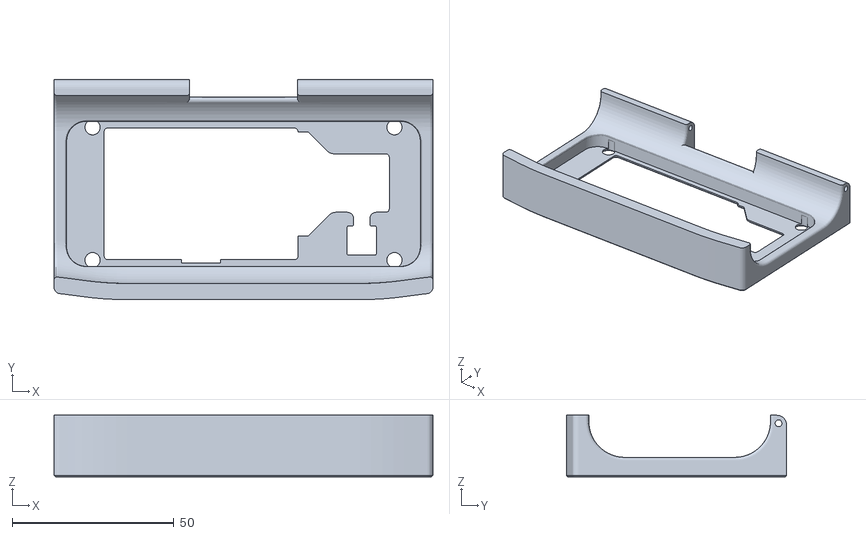
[picture p78: CAD file, 2023-03-27]
Type-V/STLs/Skirt/PreBuild_Parts/Screen/mini12864_case_front.stl
117.0 x 68.0 x 19.0
