Vprince099/ZANDVE/Type-V/STLs/Tension_Towers/Left/L_Tensioner_Knob[acc].stl

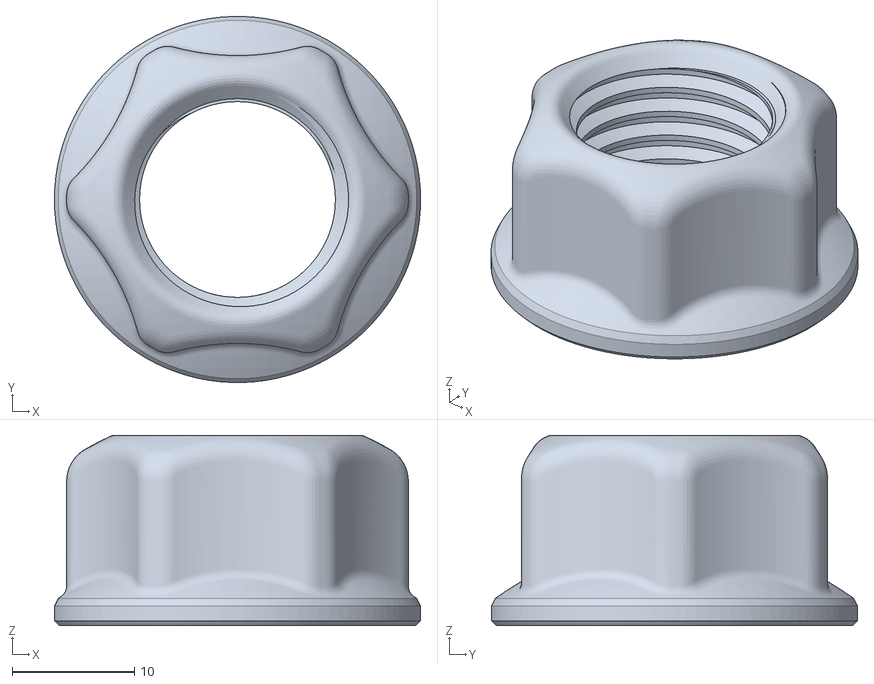
[picture p79: CAD file, 2023-03-27]
Type-V/STLs/Tension_Towers/Left/L_Tensioner_Knob[acc].stl
30.0 x 30.0 x 15.6
