Vprince099/ZANDVE/Type-V/STLs/Top_Hat_STD/TH_Front_Left/FL Unlock Pin[acc].stl

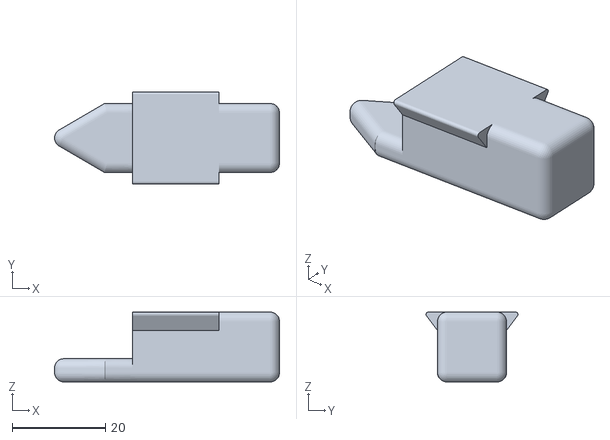
[picture p80: CAD file, 2023-03-26]
Type-V/STLs/Top_Hat_STD/TH_Front_Left/FL Unlock Pin[acc].stl
48.3 x 19.7 x 15.0
