Vprince099/ZANDVE/Type-V/STLs/Top_Hat_STD/TH_Front_Right/FR Lock Pin[acc].stl

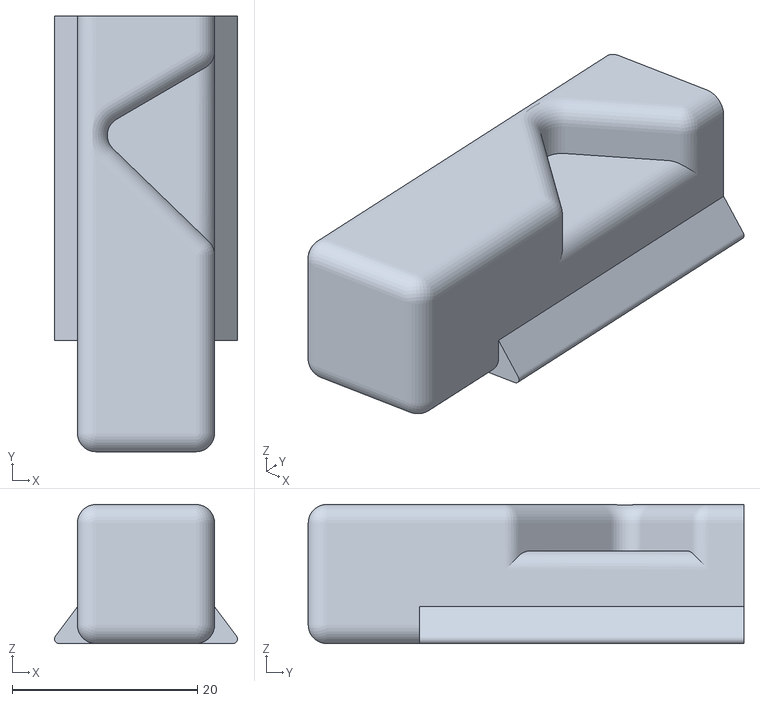
[picture p81: CAD file, 2023-03-26]
Type-V/STLs/Top_Hat_STD/TH_Front_Right/FR Lock Pin[acc].stl
19.7 x 47.0 x 15.0
