Vprince099/ZANDVE/Type-V/STLs/Top_Hat_STD/TH_Rear/Rear Panel - Center.stl

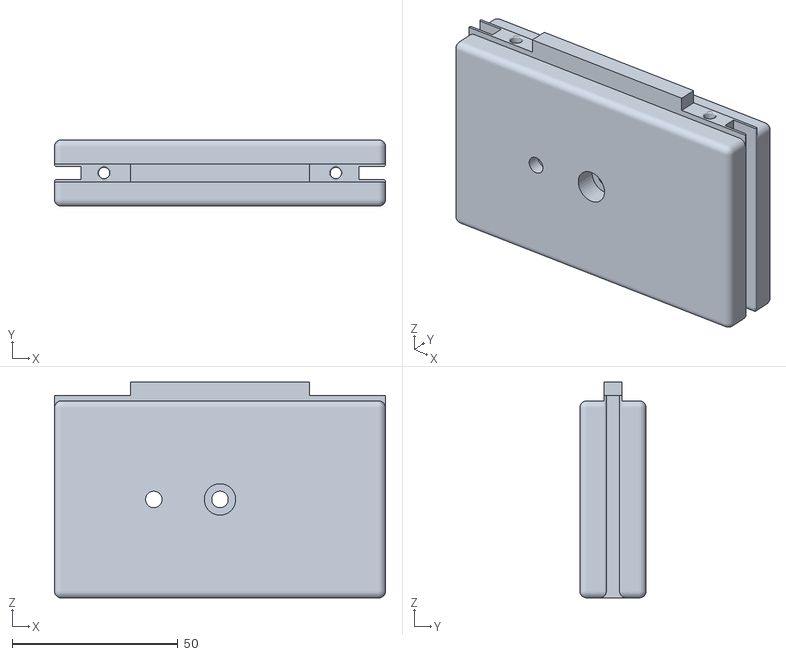
[picture p82: CAD file, 2023-03-26]
Type-V/STLs/Top_Hat_STD/TH_Rear/Rear Panel - Center.stl
100.0 x 20.0 x 65.2
