Vprince099/ZANDVE/Type-V/STLs/Top_Hat_STD/TH_Rear_Right/RR Base.stl

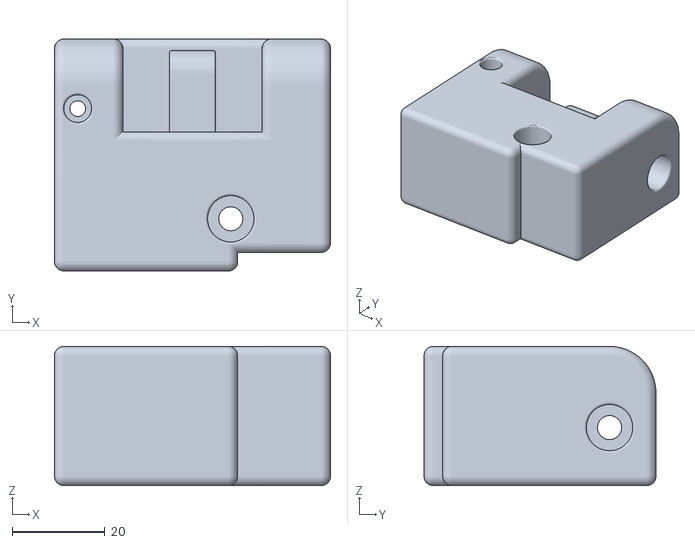
[picture p83: CAD file, 2023-03-26]
Type-V/STLs/Top_Hat_STD/TH_Rear_Right/RR Base.stl
59.5 x 50.0 x 30.0
