Vprince099/ZANDVE/Type-V/STLs/Top_Hat_XL/TH_Front_Right/FR Corner.stl

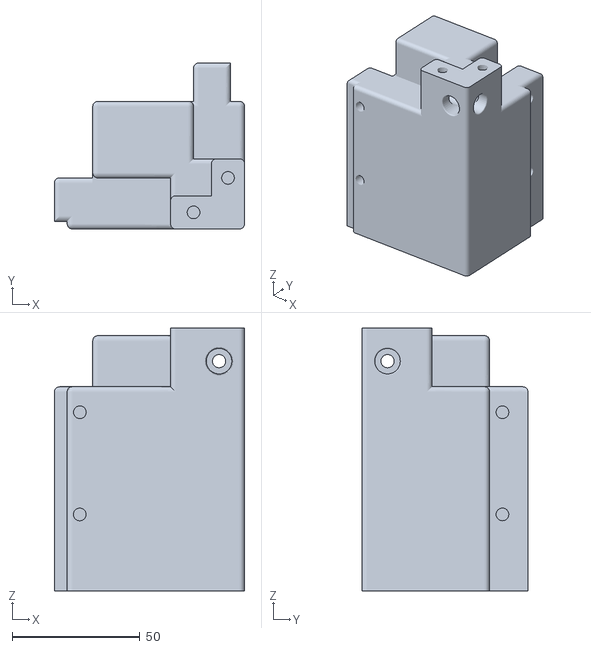
[picture p84: CAD file, 2023-04-01]
Type-V/STLs/Top_Hat_XL/TH_Front_Right/FR Corner.stl
74.5 x 65.0 x 103.0
