Vprince099/ZANDVE/Type-V/STLs/Top_Hat_XL/TH_Rear_Right/RR Panel Base.stl

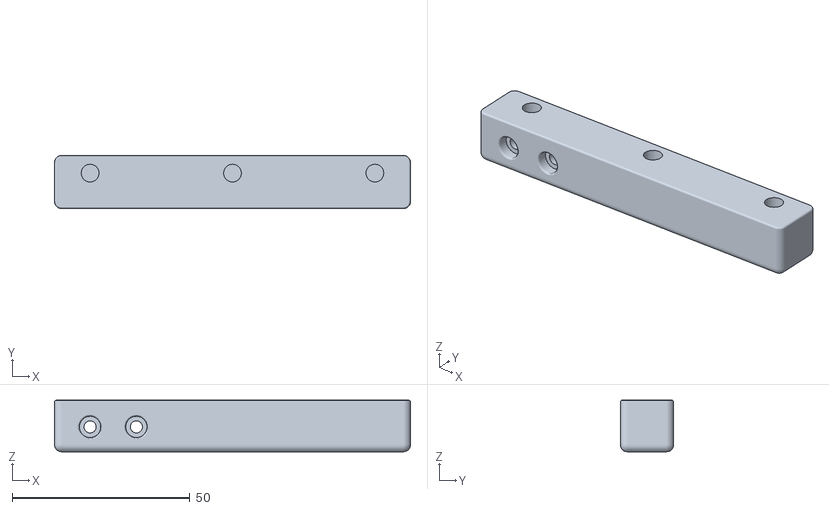
[picture p85: CAD file, 2023-04-01]
Type-V/STLs/Top_Hat_XL/TH_Rear_Right/RR Panel Base.stl
100.0 x 15.0 x 14.5
