Vprince099/ZANDVE/Type-V/STLs/Z_Motion/z_motor_mount_x2.stl

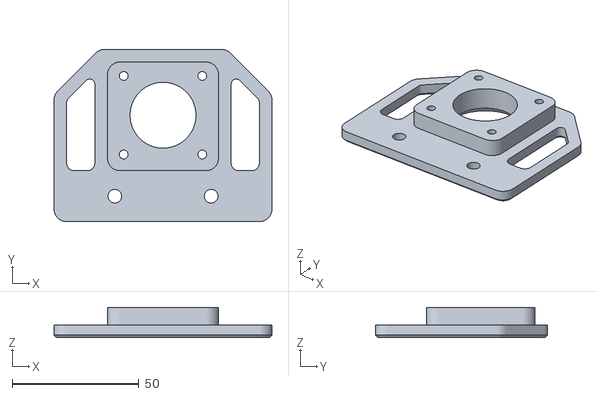
[picture p86: CAD file, 2023-03-27]
Type-V/STLs/Z_Motion/z_motor_mount_x2.stl
86.0 x 68.0 x 12.0
