Vprince099/ZANDVE/Type-Z/STLs/Panels/Gantry/Rear/Rear Panel Lid - Left[acc].stl

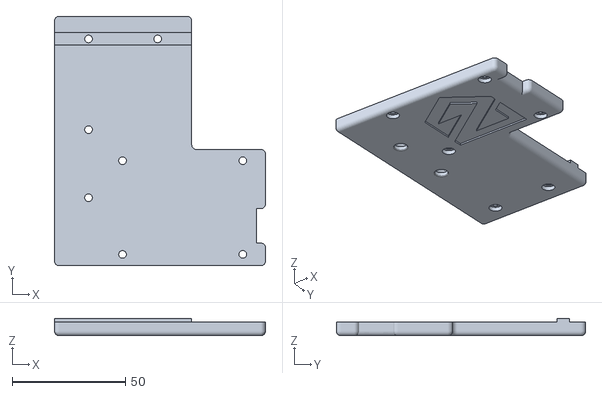
[picture p87: CAD file, 2023-03-26]
Type-Z/STLs/Panels/Gantry/Rear/Rear Panel Lid - Left[acc].stl
93.0 x 110.0 x 7.70
