Vprince099/ZANDVE/Type-Z/STLs/Rear_Steppers/Max Power/Right/R Frame Top Plate.stl

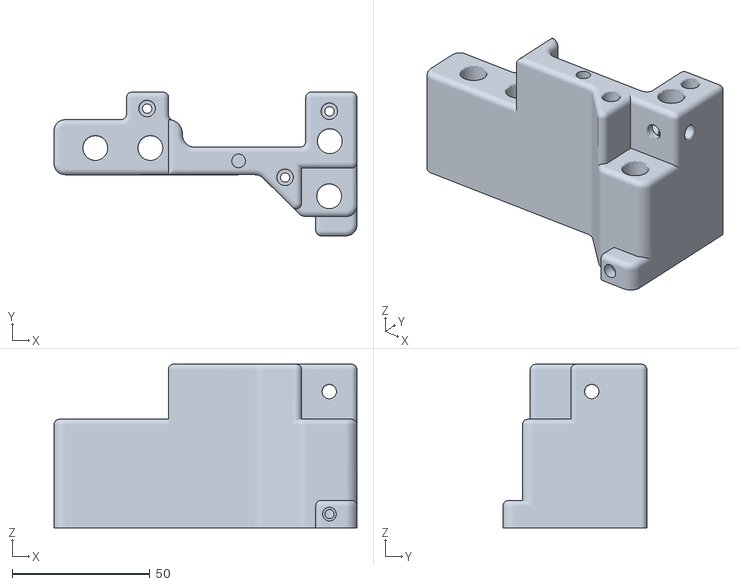
[picture p88: CAD file, 2023-03-26]
Type-Z/STLs/Rear_Steppers/Max Power/Right/R Frame Top Plate.stl
110.0 x 52.2 x 59.5
