Vprince099/ZANDVE/Type-Z/STLs/Skirt/PostBuild_Parts/Front/Skirt_E5+_Front_Left.stl

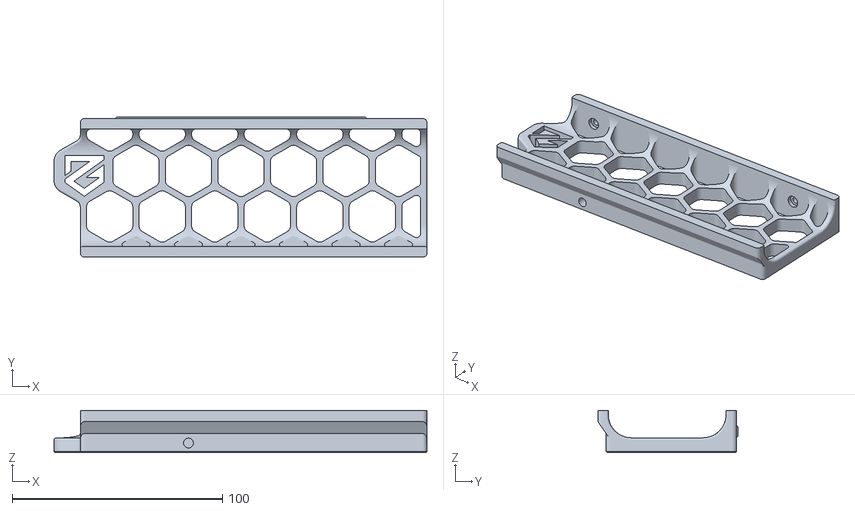
[picture p89: CAD file, 2023-03-27]
Type-Z/STLs/Skirt/PostBuild_Parts/Front/Skirt_E5+_Front_Left.stl
177.5 x 66.8 x 20.0
