Vprince099/ZANDVE/Type-V/STLs/Backpack_Enclosure/backpack_base_left.stl

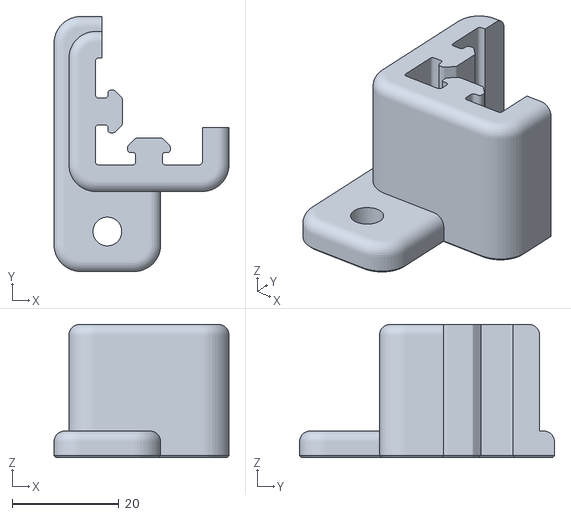
[picture p90: CAD file, 2023-03-27]
Type-V/STLs/Backpack_Enclosure/backpack_base_left.stl
32.8 x 47.8 x 25.0
