Vprince099/ZANDVE/Type-V/STLs/Electronics/skr_1.3_bracket_horizontal.stl

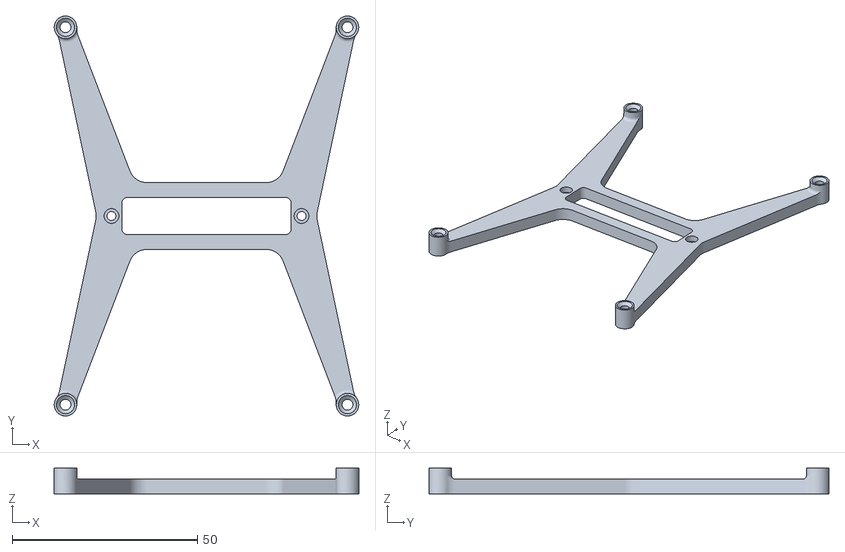
[picture p91: CAD file, 2023-03-27]
Type-V/STLs/Electronics/skr_1.3_bracket_horizontal.stl
82.2 x 107.9 x 7.00
