Vprince099/ZANDVE/Type-V/STLs/Limit_Switch_Mounts/Cable Chain Bridge_Y Limit.stl

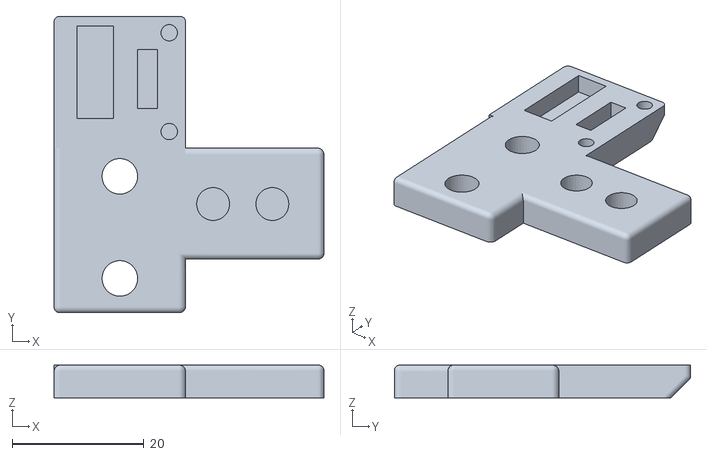
[picture p92: CAD file, 2023-03-27]
Type-V/STLs/Limit_Switch_Mounts/Cable Chain Bridge_Y Limit.stl
41.0 x 45.0 x 5.00
