Vprince099/ZANDVE/Type-V/STLs/Panels/Gantry/Left/Rear Panel Base.stl

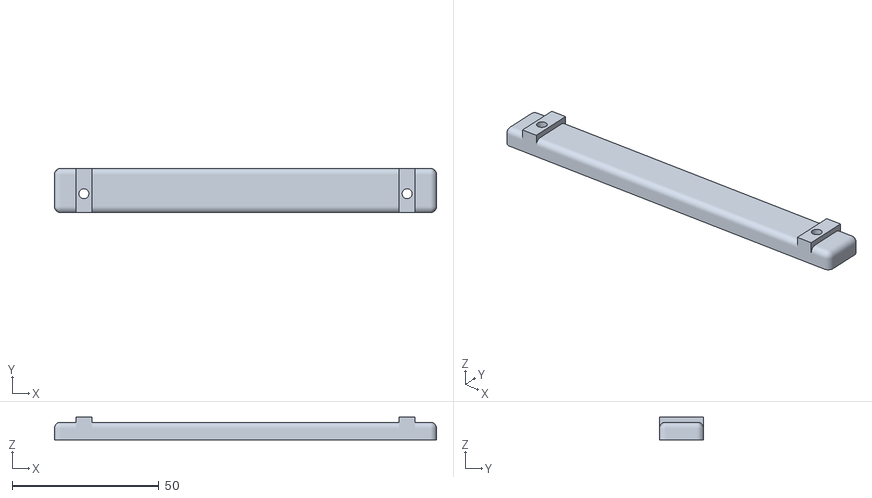
[picture p93: CAD file, 2023-03-26]
Type-V/STLs/Panels/Gantry/Left/Rear Panel Base.stl
130.0 x 15.0 x 7.75
