Vprince099/ZANDVE/Type-V/STLs/Skirt/PostBuild_Parts/Sides/[a]_fan_grill_retainer_x2.stl

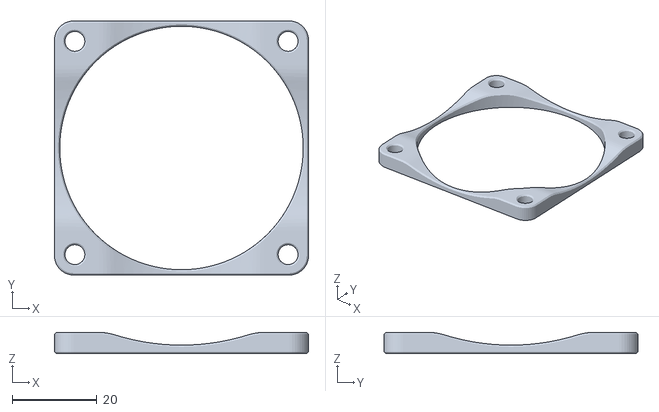
[picture p94: CAD file, 2023-03-27]
Type-V/STLs/Skirt/PostBuild_Parts/Sides/[a]_fan_grill_retainer_x2.stl
60.0 x 60.0 x 5.00
