Vprince099/ZANDVE/Type-V/STLs/Skirt/PreBuild_Parts/Screen/[a]_btt_knob_light_shield.stl

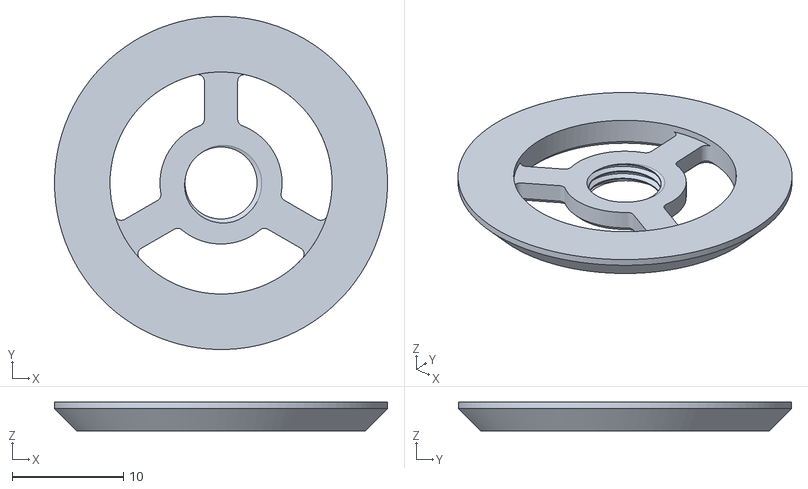
[picture p95: CAD file, 2023-03-27]
Type-V/STLs/Skirt/PreBuild_Parts/Screen/[a]_btt_knob_light_shield.stl
30.0 x 30.0 x 2.60
